tonykoop/ashiko-drum-workshop/images/05-glue-up-cherry-staves.jpg

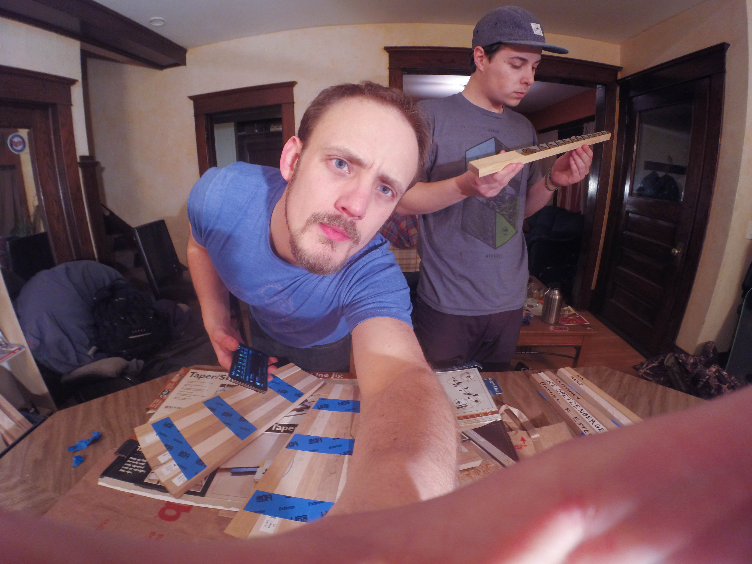
images/05-glue-up-cherry-staves.jpg
