tonykoop/ashiko-drum-workshop/images/05b-glue-up-clamping.jpg

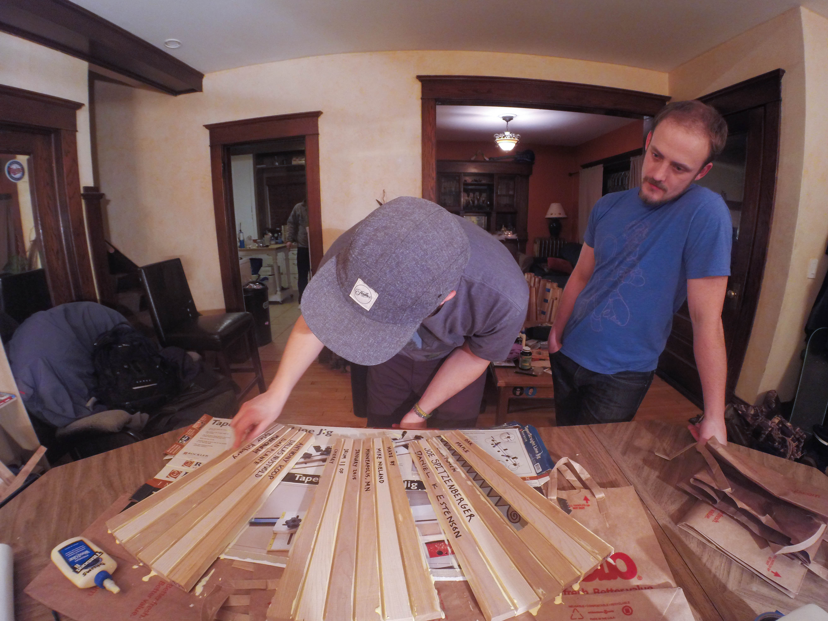
images/05b-glue-up-clamping.jpg
