tonykoop/ashiko-drum-workshop/images/2021-09-15 13.05.39.jpg

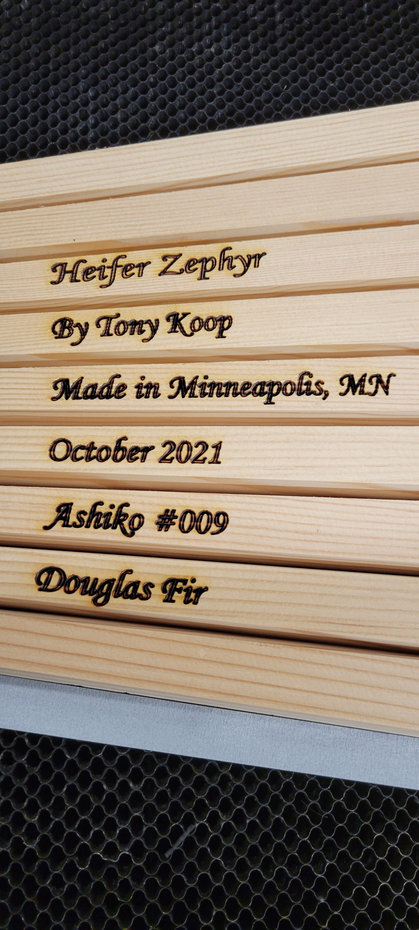
images/2021-09-15 13.05.39.jpg
