tonykoop/ashiko-drum-workshop/images/2021-10-07 13.28.02.jpg

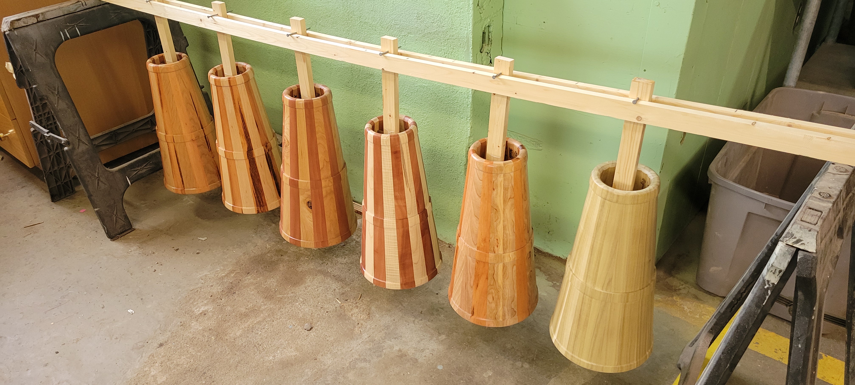
images/2021-10-07 13.28.02.jpg
