tonykoop/ashiko-drum-workshop/images/2021-10-21 14.14.43.jpg

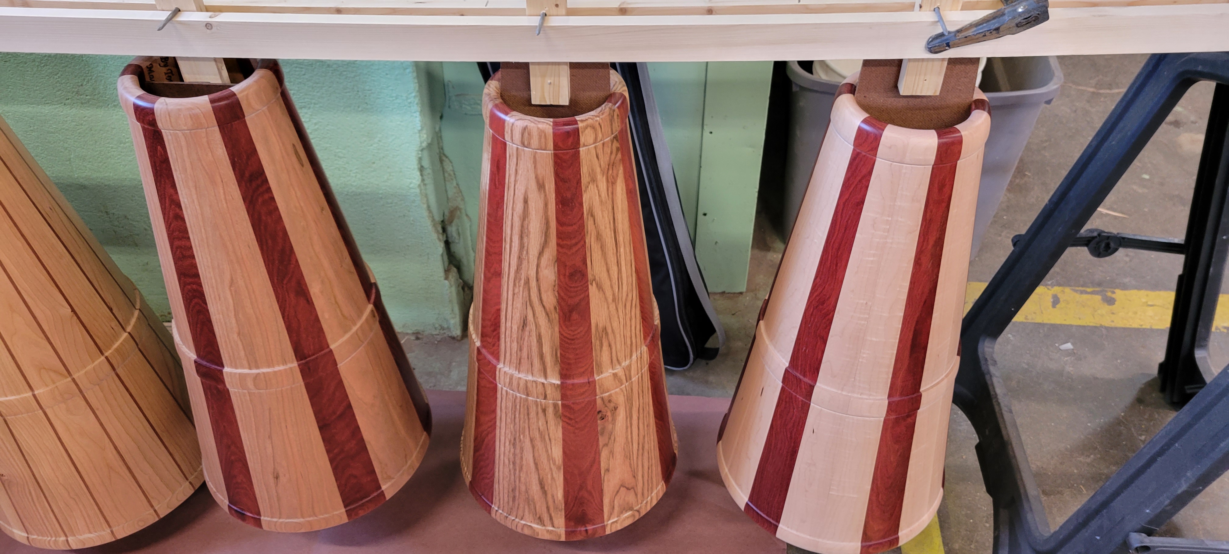
images/2021-10-21 14.14.43.jpg
