tonykoop/ashiko-drum-workshop/images/2021-10-22 16.16.47.jpg

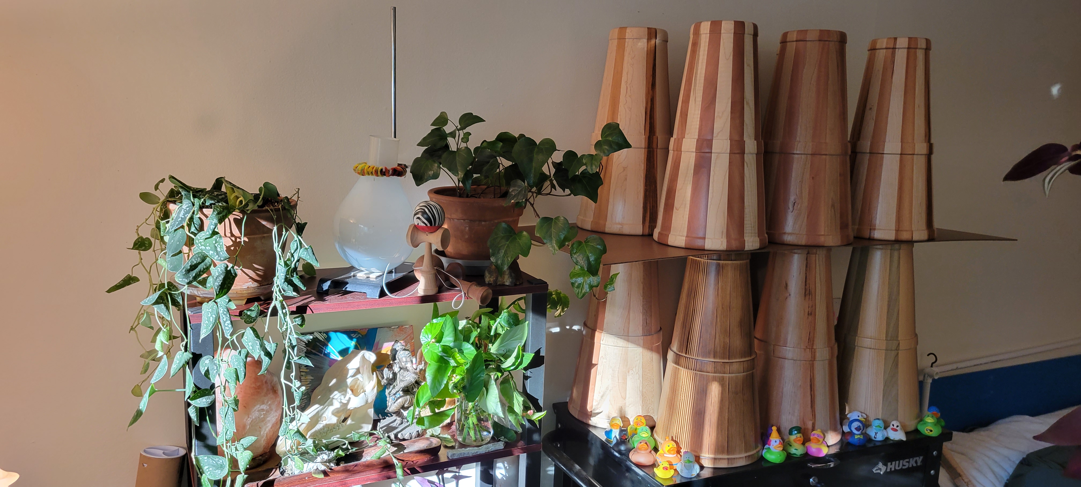
images/2021-10-22 16.16.47.jpg
