tonykoop/ashiko-drum-workshop/images/2021-10-22 16.17.06.jpg

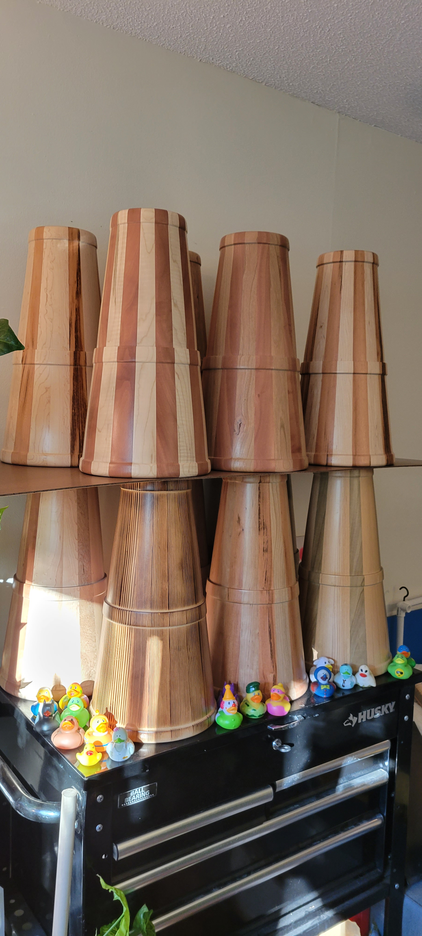
images/2021-10-22 16.17.06.jpg
