tonykoop/ashiko-drum-workshop/images/2021-12-14 12.53.09.jpg

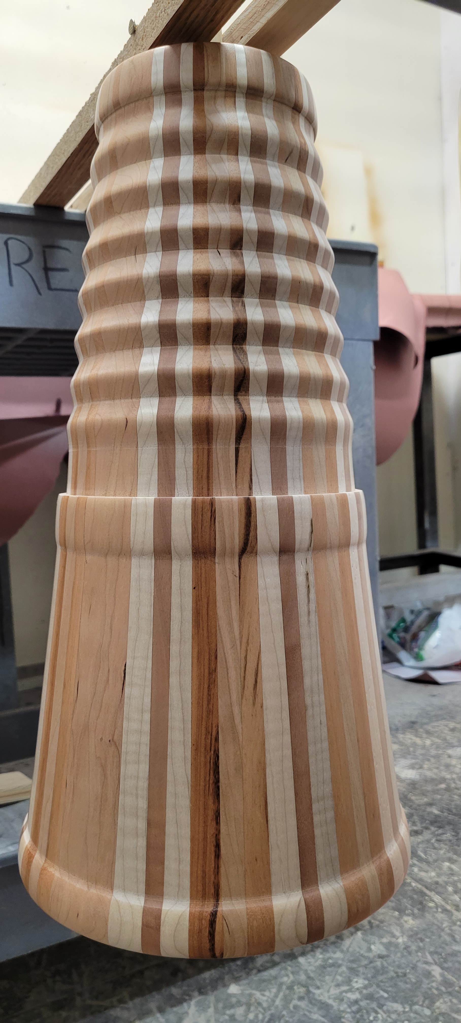
images/2021-12-14 12.53.09.jpg
