tonykoop/ashiko-drum-workshop/images/20211008_104015.jpg

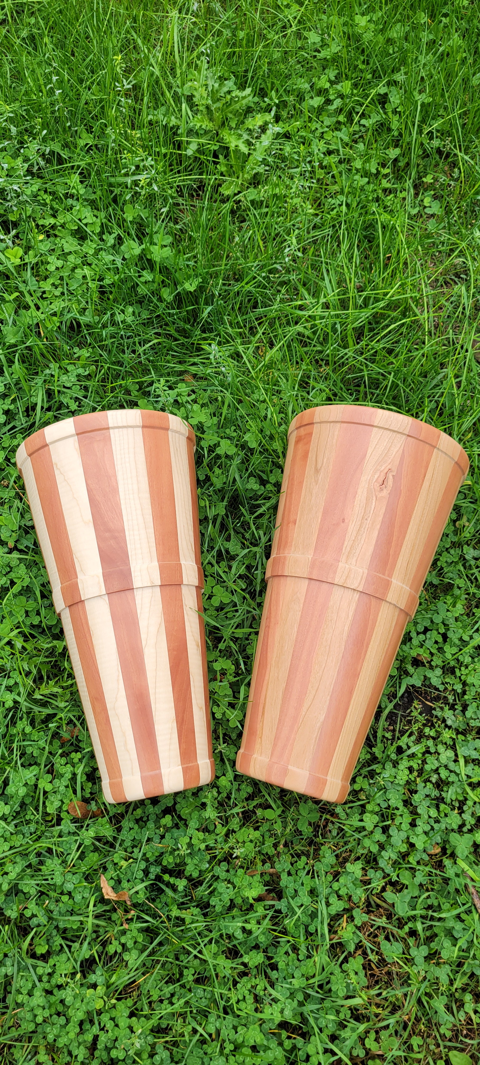
images/20211008_104015.jpg
