tonykoop/ashiko-drum-workshop/images/Ashiko Stave 3 Nesting.JPG

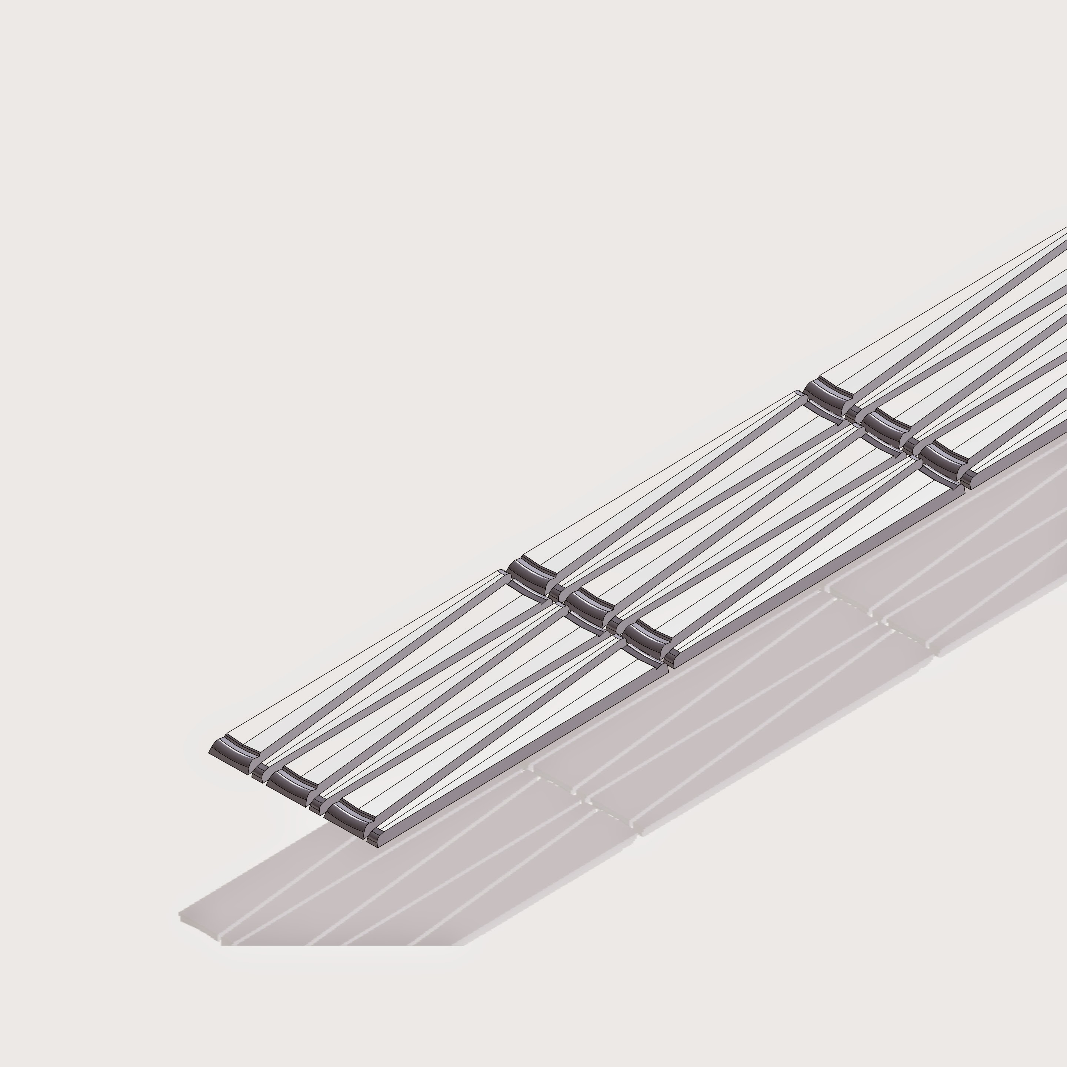
images/Ashiko Stave 3 Nesting.JPG
