tonykoop/ashiko-drum-workshop/images/figure-stave-labeling.png

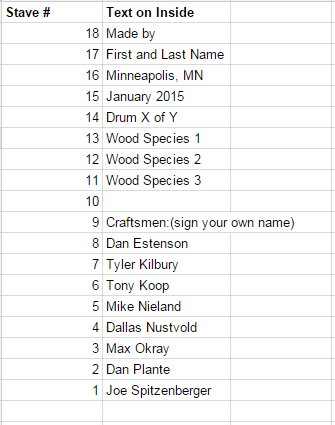
images/figure-stave-labeling.png
