tonykoop/ashiko-drum-workshop/images/Hack Factory Turning - Part 2 -1.JPG

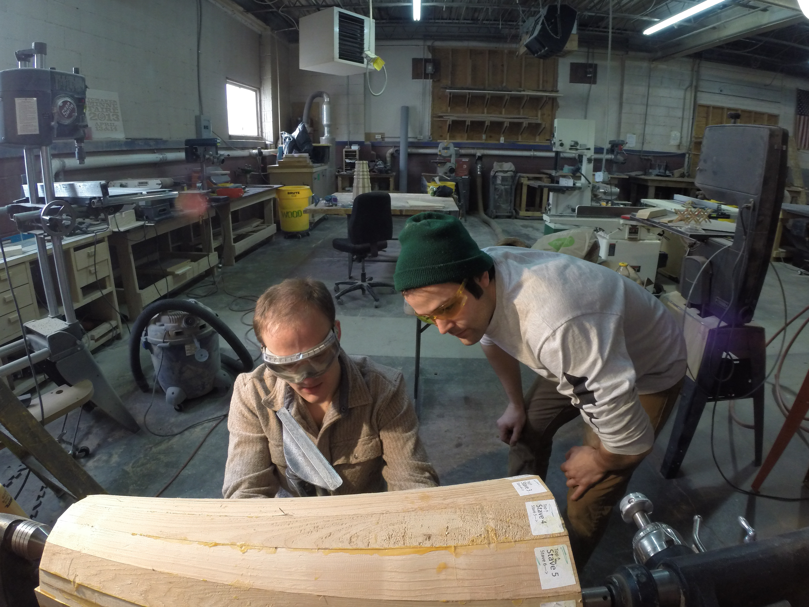
images/Hack Factory Turning - Part 2 -1.JPG
