tonykoop/ashiko-drum-workshop/images/Hack Factory Turning - Part 2 -23.JPG

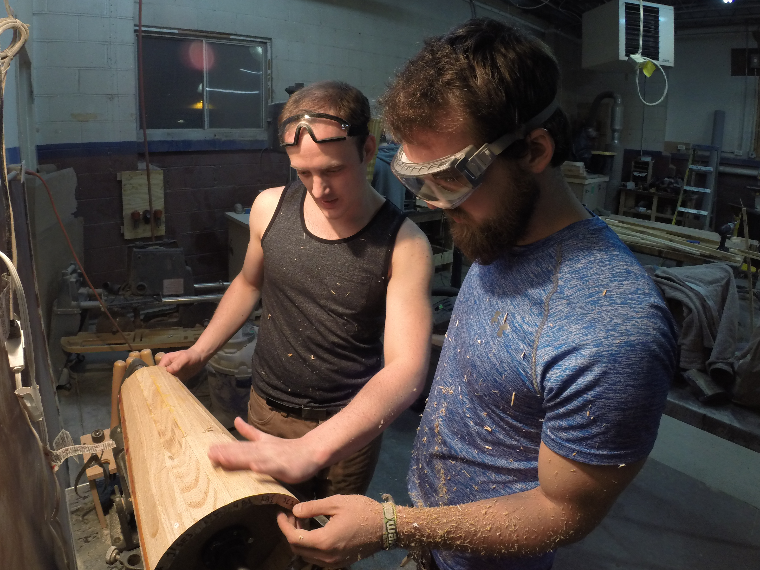
images/Hack Factory Turning - Part 2 -23.JPG
