tonykoop/ashiko-drum-workshop/images/Hack Factory Turning-49.JPG

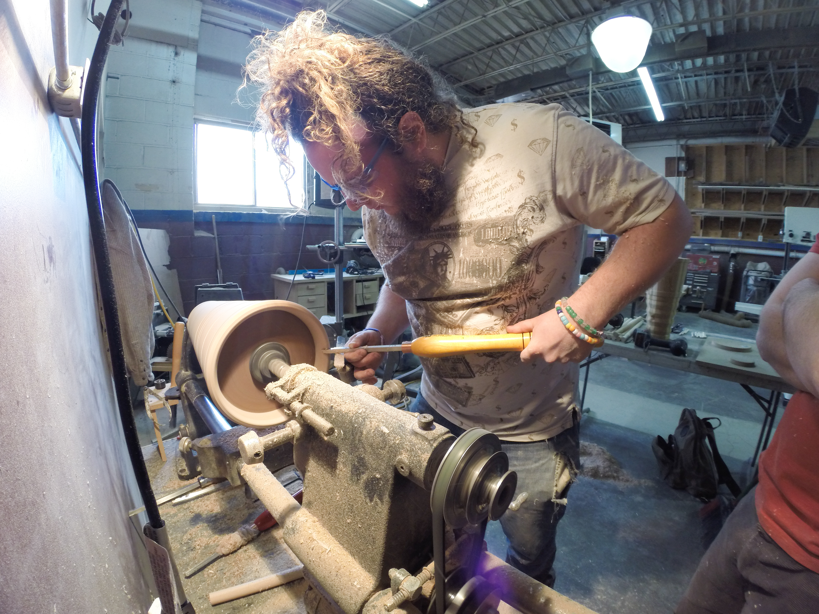
images/Hack Factory Turning-49.JPG
