tonykoop/ashiko-drum-workshop/images/IMG_20170116_170506.jpg

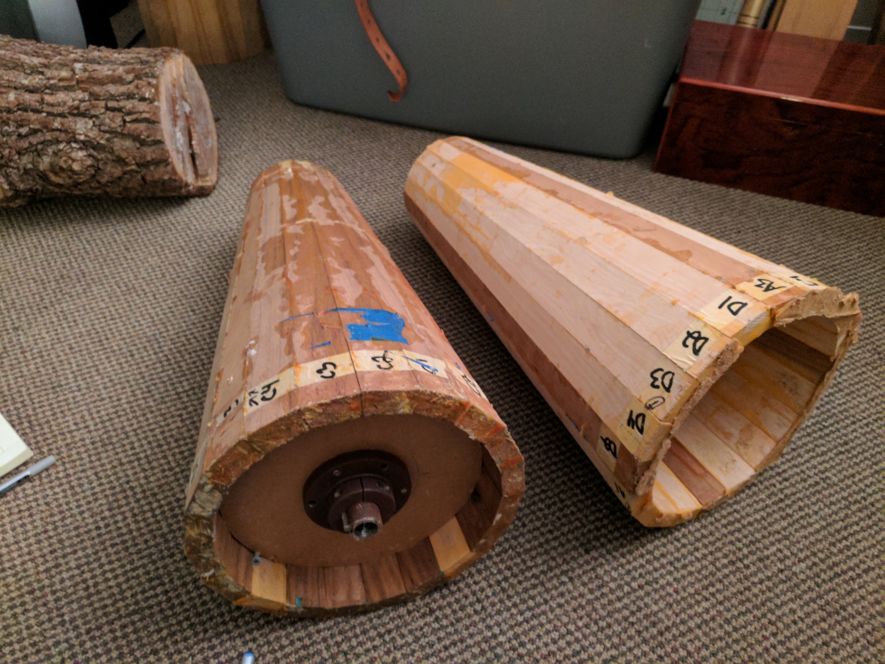
images/IMG_20170116_170506.jpg
