tonykoop/ashiko-drum-workshop/images/macro/multi-wood-stave-seams.png

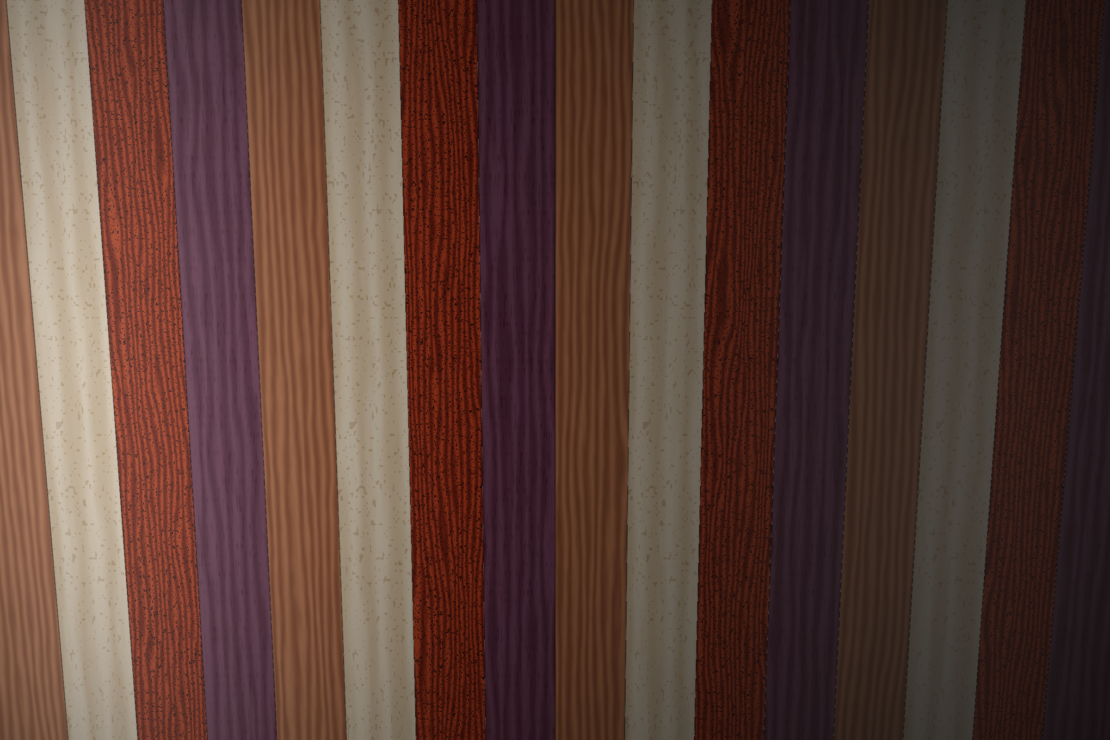
images/macro/multi-wood-stave-seams.png
