tonykoop/ashiko-drum-workshop/images/macro/rope-laced-goatskin-head.png

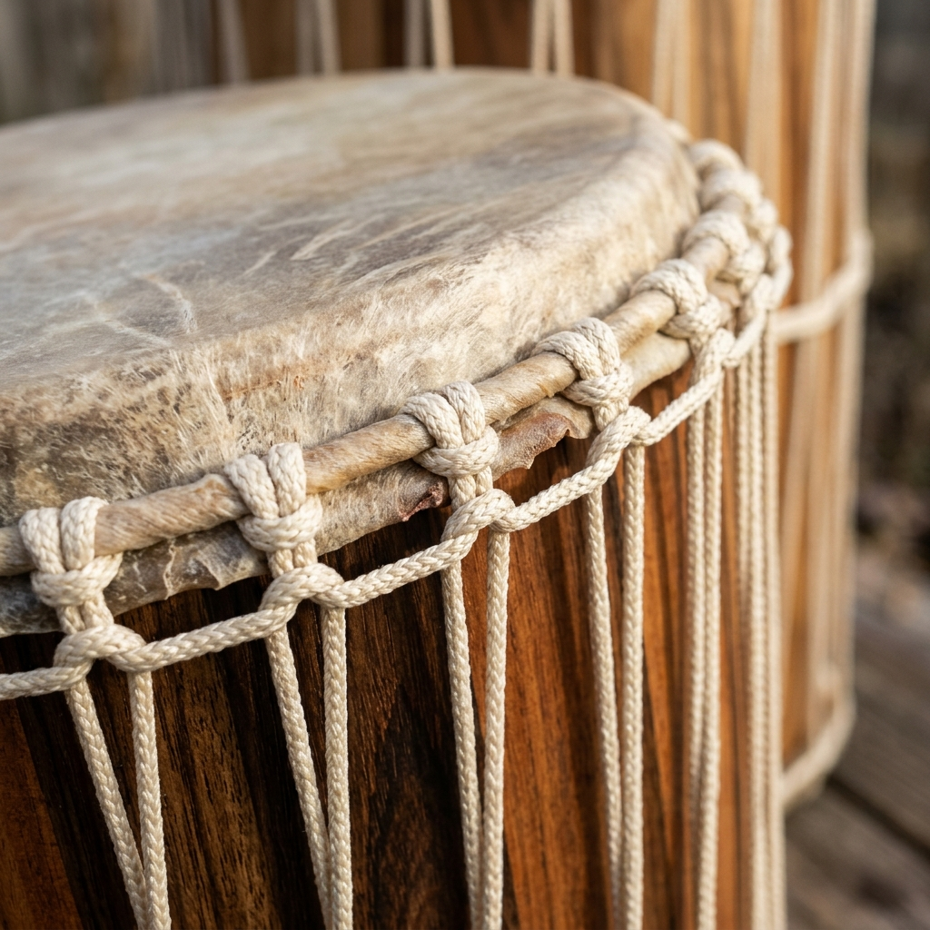
images/macro/rope-laced-goatskin-head.png
