tonykoop/ashiko-drum-workshop/images/Mike on Lathe-11.jpg

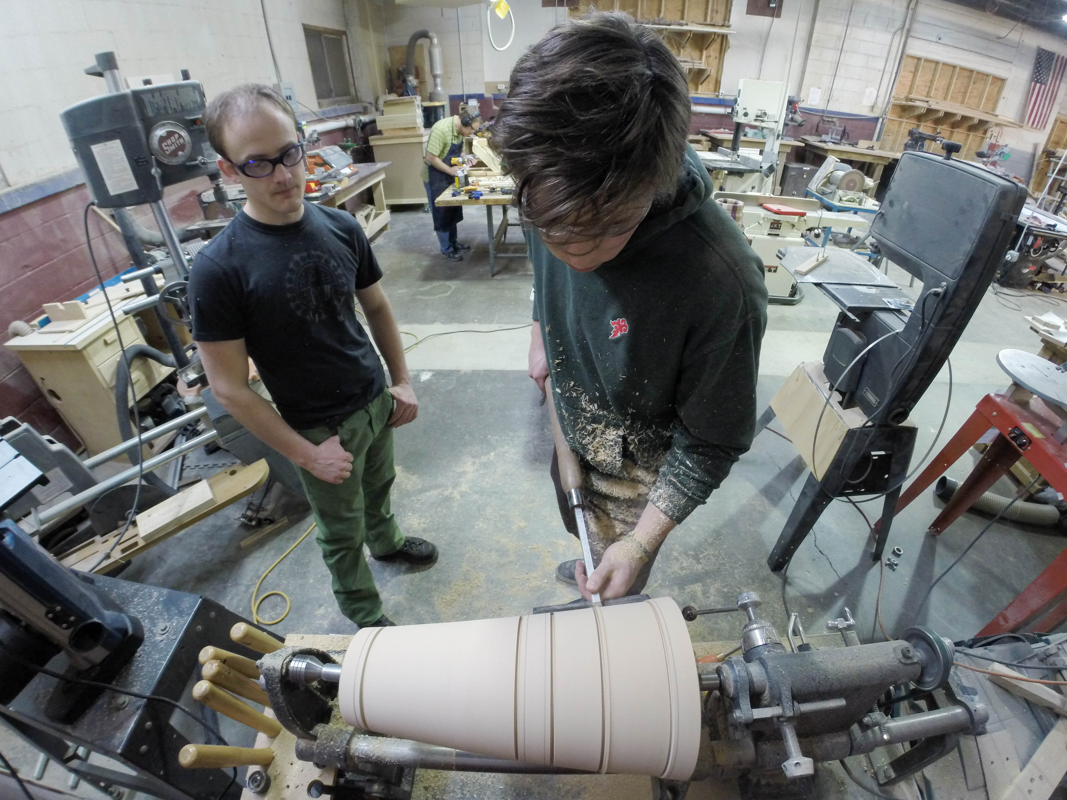
images/Mike on Lathe-11.jpg
