tonykoop/ashiko-drum-workshop/docs/Ashiko Makers Club/PDFs/Ashiko - BOM.pdf

Assembly Name :18 Stave Hardwood Ashiko | [42]
Serial Number:WFTH-55XXX-mmddyy-AA
Quote Date: | 11/19/2014
Estimated High Cost : | $158.00
Estimated Low Cost : | $77.50

# Ashiko Hand Drum

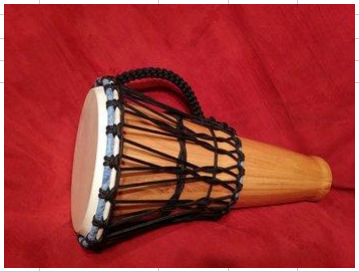
[picture p24: figure]

Part # Part Name | Description | Qty | Units | Picture | High Est | High Cost | Low Est | Low Cost

1

8/4 Hardwood
Lumber

Dried and surfaced
hardwood of various sorts
including domestic and
imported species.
5.3 | Board Feet | $ 10.00 | $ 53.00 | $ 5.00 | $ 26.50
2 | Steel Ring

Prefabricated 1/4" steel
ring. One small ring for the bottom and two larger rings for the top.
3 | Rings | $ 8.00 | $ 24.00 | $ 4.00 | $ 12.00
3 | Goat Skin

Hairless goat skin large
enough to fit the diameter of the drum head.
1 | Goat | $ 20.00 | $ 20.00 | $ 11.00 | $ 11.00
4 | Polyester Rope

3/16" double-braided
polyester with a lowstretch core, various color options available.
100 | Feet | $ 0.20 | $ 20.00 | $ 0.10 | $ 10.00
5 | Fabric

2" strip of decorative fabric used to wrap the top and
bottom steel rings.
60 | Inches | $ 0.10 | $ 6.00 | $ 0.05 | $ 3.00
6 | Supplies | Sandpaper, wood glue,
lacquer | 1 | $ 10.00 | $ 10.00 | $ 5.00 | $ 5.00

7

Shipping &
Handling | 1 | $ 25.00 | $ 25.00 | $ 10.00 | $ 10.00
Notes: | Total | $ 158.00 | $ 77.50
~Purchase lumber at Wood From The Hood
~The first four characters of the serial number decode as Wood From The Hood
followed by the 5 digit zip code where the wood originally grew, mmddyy is the date
the drum shell was glued together followed by the drum makers initials.
~Species available: Ash, Black Walnut, Butternut, Cherry, Elm
