tonykoop/ashiko-drum-workshop/docs/Ashiko Makers Club/PDFs/Bill of Materials V2.pdf

Assembly Name :18 Stave Hardwood Ashiko | [42]

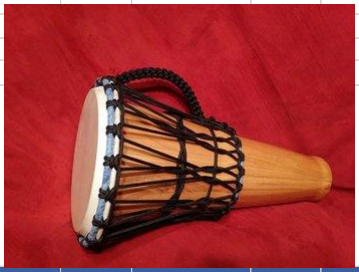
[picture p25: figure]

Quote Date: | 12/26/2014
Estimated Cost : | $78.00 | *

# Ashiko Hand Drum

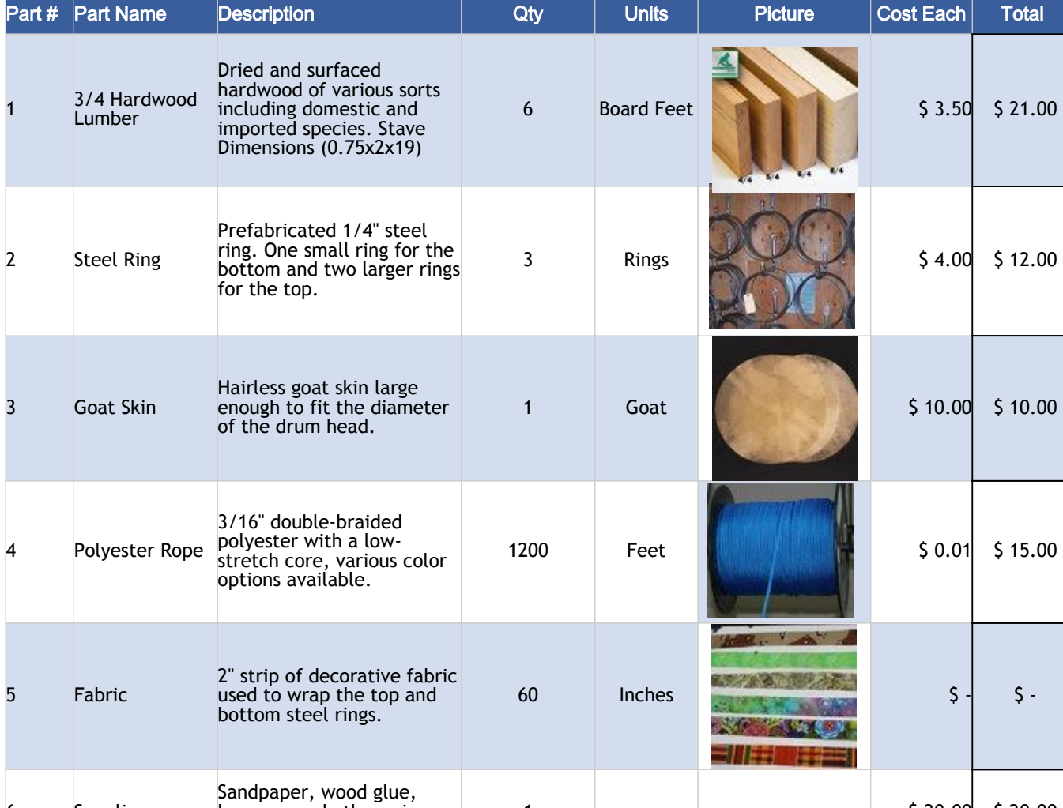
[picture p26: figure]
Part # Part Name; Description; Qty; Units; Picture; Cost Each; Total; 3/4 Hardwood Lumber; Dried and surfaced hardwood of various sorts including domestic and imported species. Stave Dimensions (0.75x2x19); Board Feet; Steel Ring; Prefabricated 1/4" steel ring. One small ring for the bottom and two larger rings for the top.; Rings; Goat Skin; Hairless goat skin large enough to fit the diameter of the drum head.; Goat; Polyester Rope; 3/16" double-braided polyester with a low- stretch core, various color options available.; Feet; Fabric; 2" strip of decorative fabric used to wrap the top and bottom steel rings.; Inches; Sandpaper, wood glue,

6 | Supplies

lacquer, and other misc
supplies.
1 | $ 20.00 | $ 20.00
Notes: | Total | $ 78.00
~3/4" Lumber Purchased @ Youngblood Lumber Company:
~5: Cherry (Ch) 5: Hard Maple (HM) | 1: Padauk (Pd) 1: Purple Heart (Ph)
*Price based on bulk discount of 7 or more assemblies using Hard Maple and/or Che
