tonykoop/ashiko-drum-workshop/docs/Ashiko Makers Club/Large Block of Wood.SLDPRT

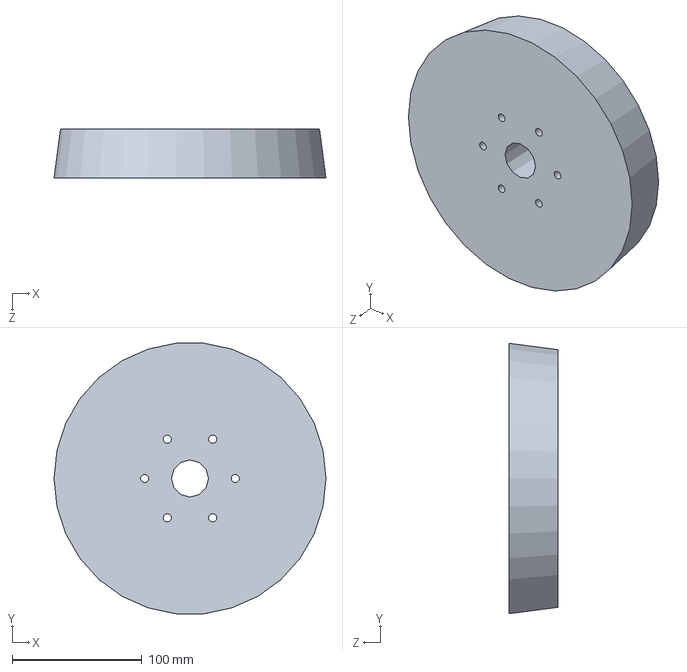
[picture p42: CAD file, 2026-05-23]
docs/Ashiko Makers Club/Large Block of Wood.SLDPRT
209.5 x 208.4 x 38.1 mm
