tonykoop/ashiko-drum-workshop/docs/Ashiko Makers Club/Spokes/16 Spoke.SLDPRT

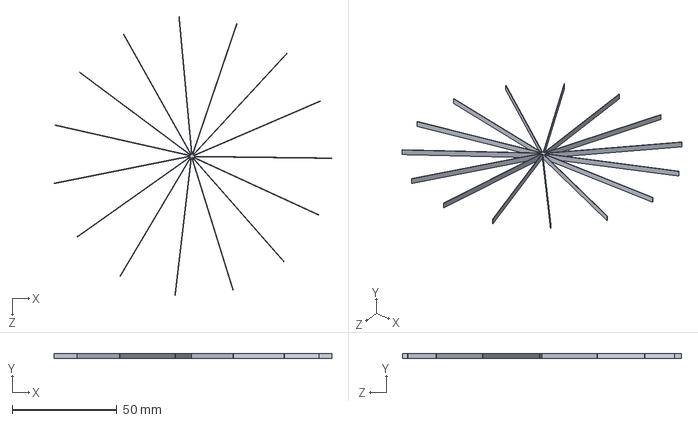
[picture p43: CAD file, 2026-05-23]
docs/Ashiko Makers Club/Spokes/16 Spoke.SLDPRT
132.8 x 2.54 x 133.3 mm
