tonykoop/ashiko-drum-workshop/docs/Ashiko Makers Club/To Print/Front Piece V4.STL

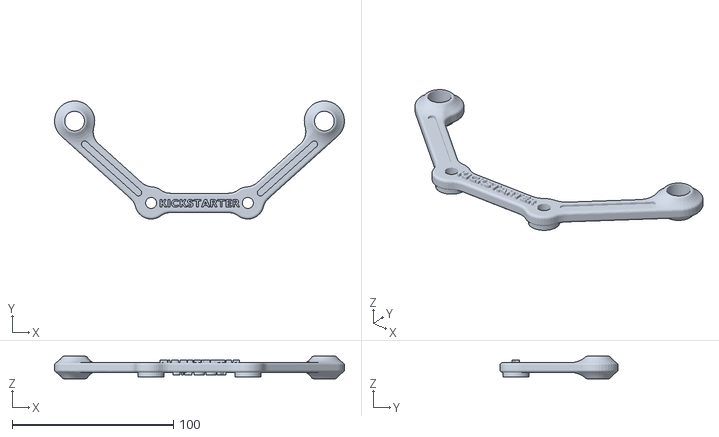
[picture p44: CAD file, 2026-05-23]
docs/Ashiko Makers Club/To Print/Front Piece V4.STL
180.0 x 73.3 x 14.0
