tonykoop/ashiko-drum-workshop/CAD/CNC Sled/Compound Taper Wedge Corrector.SLDPRT

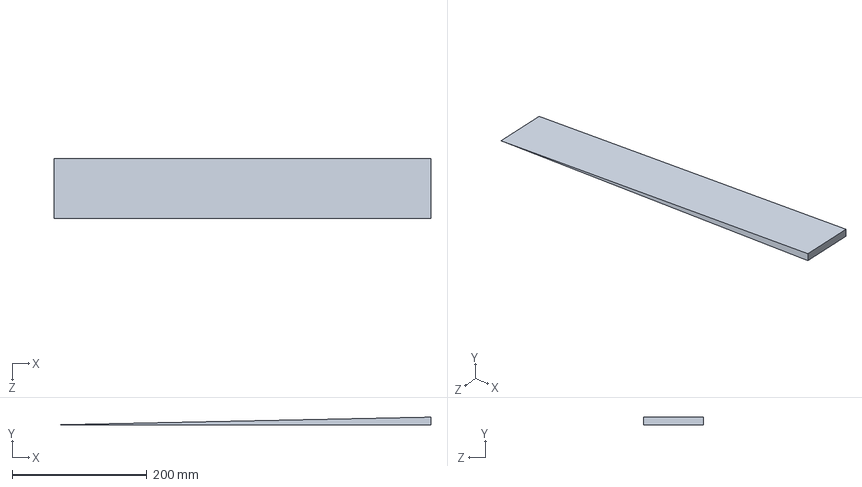
[picture p45: CAD file, 2026-05-23]
CAD/CNC Sled/Compound Taper Wedge Corrector.SLDPRT
558.8 x 11.5 x 88.9 mm
