tonykoop/ashiko-drum-workshop/docs/Ashiko Makers Club/Ashiko V3 REV010915 (Koops_Windows's conflicted copy 2015-01-16).SLDPRT

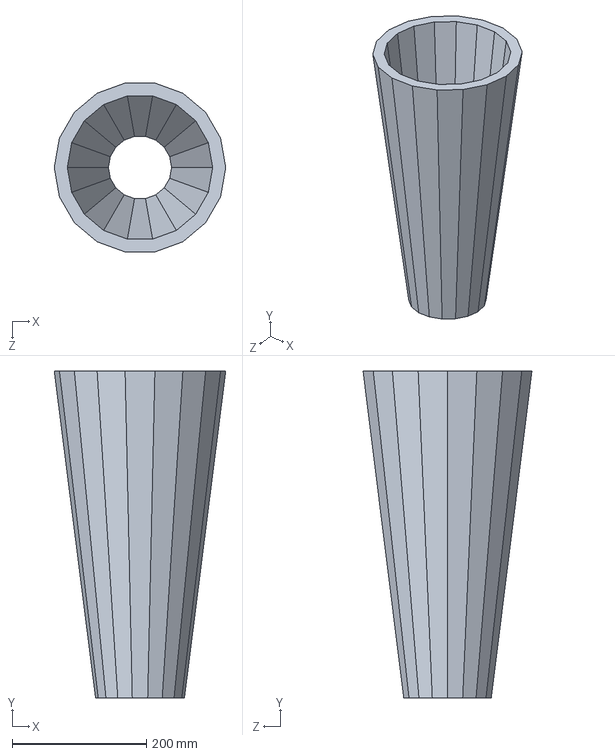
[picture p46: CAD file, 2026-05-23]
docs/Ashiko Makers Club/Ashiko V3 REV010915 (Koops_Windows's conflicted copy 2015-01-16).SLDPRT
256.0 x 488.0 x 252.1 mm
