tonykoop/ashiko-drum-workshop/docs/Ashiko Makers Club/Djembe/Djembe Joint Plate.SLDPRT

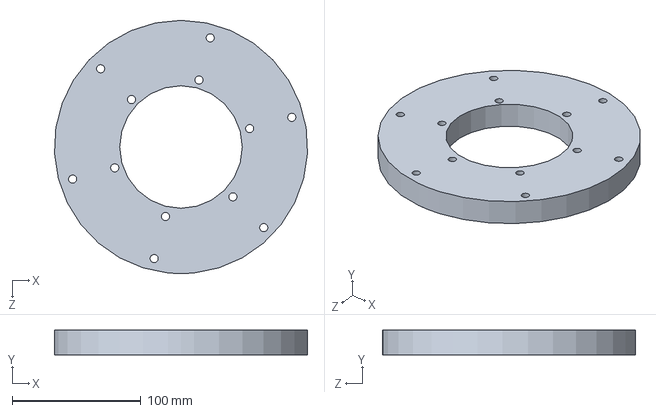
[picture p47: CAD file, 2026-05-23]
docs/Ashiko Makers Club/Djembe/Djembe Joint Plate.SLDPRT
196.6 x 19.1 x 196.9 mm
