tonykoop/ashiko-drum-workshop/docs/Ashiko Makers Club/To Print/Electronics Hub V3.STL

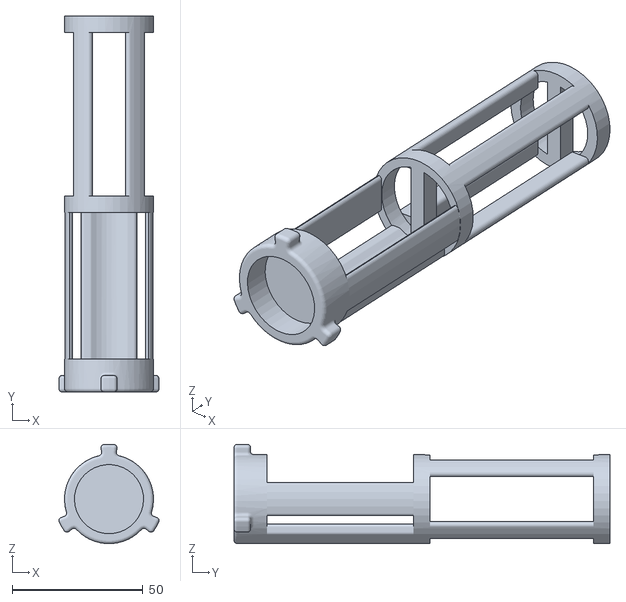
[picture p48: CAD file, 2026-05-23]
docs/Ashiko Makers Club/To Print/Electronics Hub V3.STL
38.3 x 143.8 x 38.0
