tonykoop/ashiko-drum-workshop/CAD/CNC Sled/Sled Rear A.SLDPRT

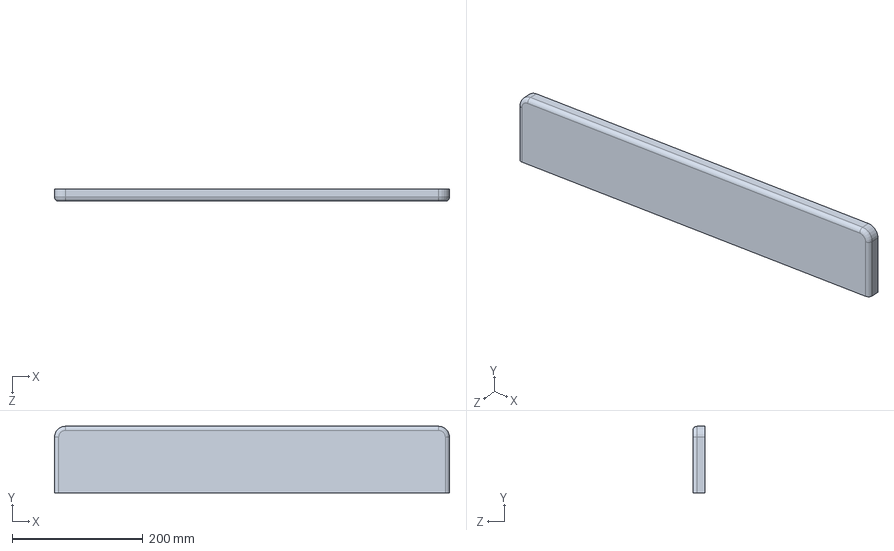
[picture p49: CAD file, 2026-05-23]
CAD/CNC Sled/Sled Rear A.SLDPRT
603.2 x 101.6 x 19.1 mm
