tonykoop/ashiko-drum-workshop/CAD/CNC Sled/Wedges/18 Segment Wedge.SLDPRT

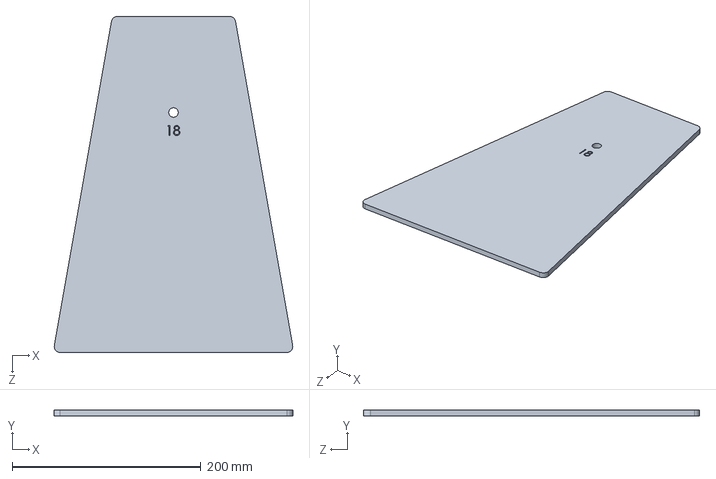
[picture p50: CAD file, 2026-05-23]
CAD/CNC Sled/Wedges/18 Segment Wedge.SLDPRT
252.5 x 5.99 x 355.6 mm
