tonykoop/ashiko-drum-workshop/docs/Ashiko Makers Club/To Print/Control Board Holder.STL

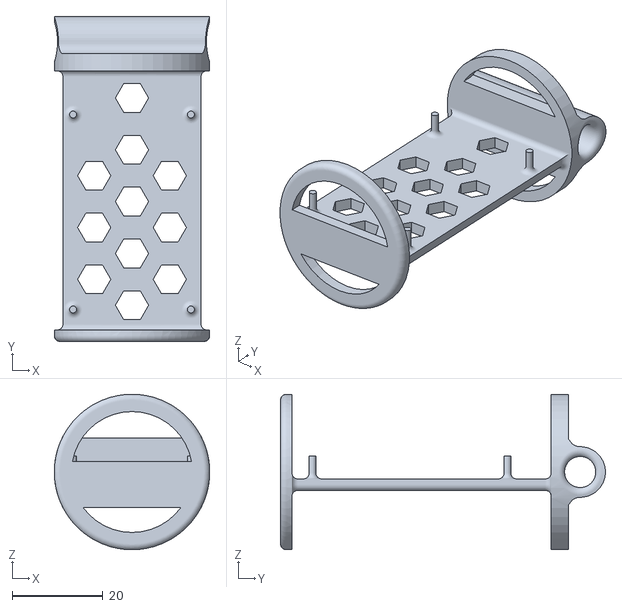
[picture p51: CAD file, 2026-05-23]
docs/Ashiko Makers Club/To Print/Control Board Holder.STL
34.3 x 71.7 x 34.3
