tonykoop/ashiko-drum-workshop/CAD/CNC Sled/3x20 Stave.SLDPRT

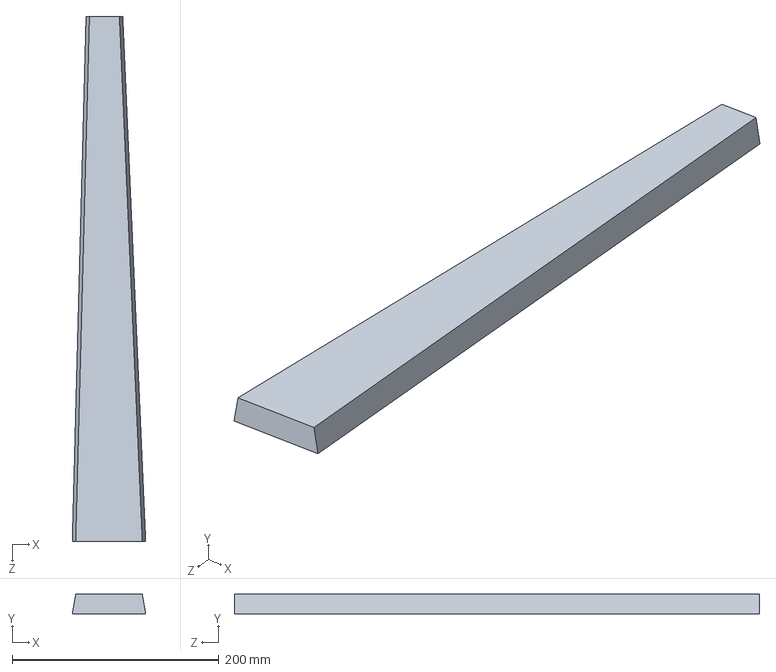
[picture p52: CAD file, 2026-05-23]
CAD/CNC Sled/3x20 Stave.SLDPRT
71.1 x 19.1 x 508.0 mm
