tonykoop/ashiko-drum-workshop/CAD/CNC Sled/Wedges/48 Segment Wedgie.SLDPRT

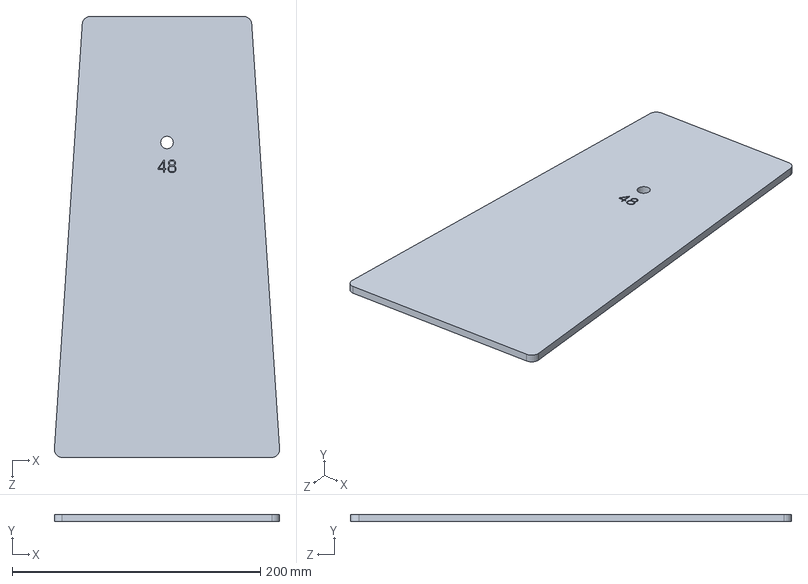
[picture p53: CAD file, 2026-05-23]
CAD/CNC Sled/Wedges/48 Segment Wedgie.SLDPRT
181.6 x 5.99 x 355.6 mm
