tonykoop/ashiko-drum-workshop/docs/Ashiko Makers Club/Djembe/Djembe Bottom REV013015.SLDPRT

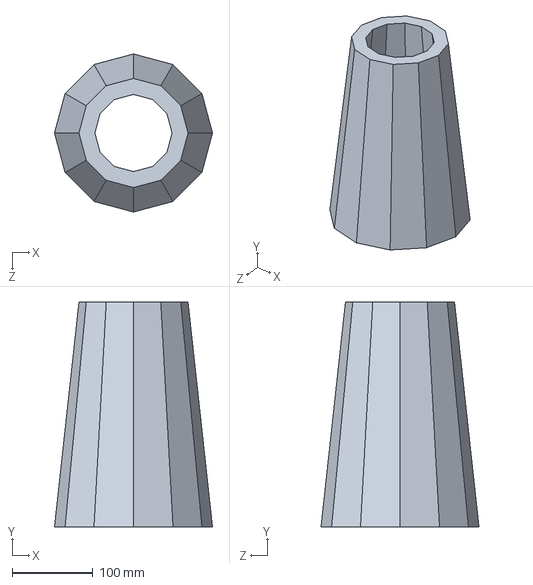
[picture p54: CAD file, 2026-05-23]
docs/Ashiko Makers Club/Djembe/Djembe Bottom REV013015.SLDPRT
196.3 x 279.4 x 196.3 mm
