tonykoop/ashiko-drum-workshop/docs/Ashiko Makers Club/To Print/Rod V4.STL

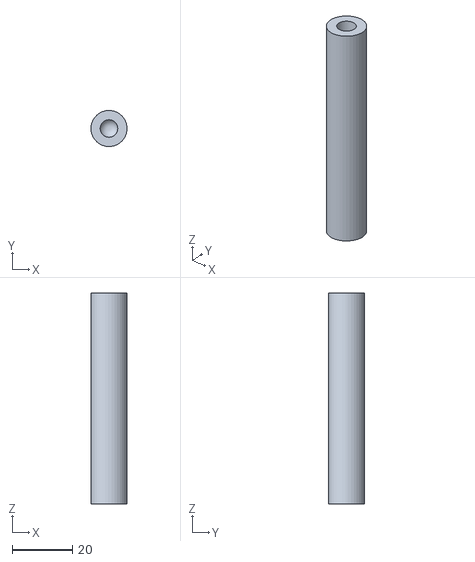
[picture p55: CAD file, 2026-05-23]
docs/Ashiko Makers Club/To Print/Rod V4.STL
12.0 x 12.0 x 70.0
