tonykoop/ashiko-drum-workshop/CAD/CNC Sled/Taper Wedge - 10 degree 18 stave shell.SLDPRT

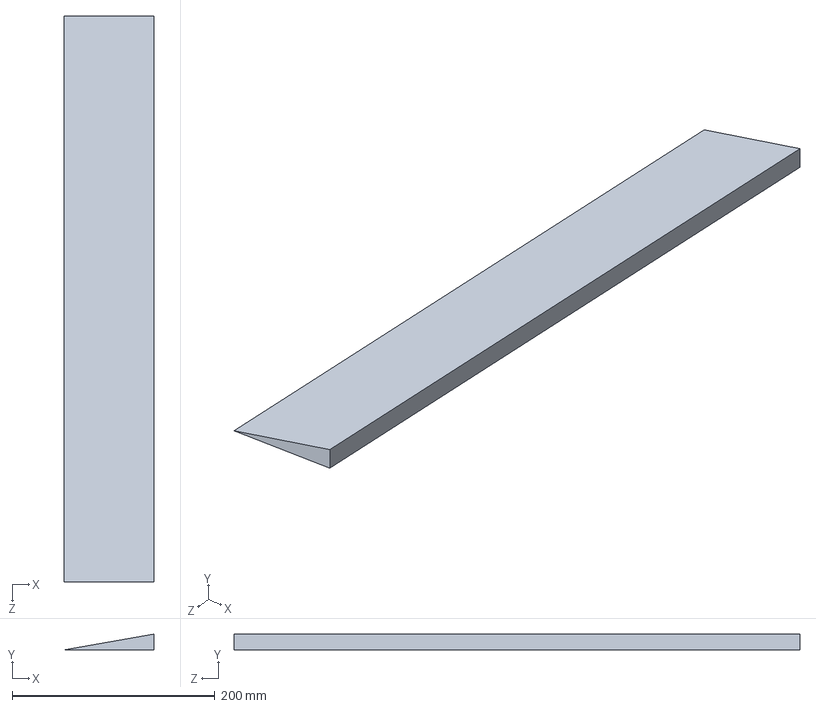
[picture p56: CAD file, 2026-05-23]
CAD/CNC Sled/Taper Wedge - 10 degree 18 stave shell.SLDPRT
88.9 x 15.7 x 558.8 mm
