tonykoop/ashiko-drum-workshop/CAD/CNC Sled/Wedges/Universal Wedge B.SLDPRT

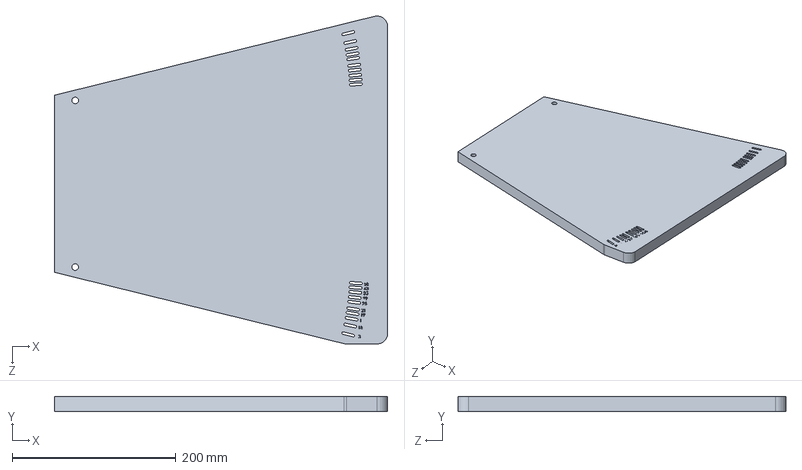
[picture p57: CAD file, 2026-05-23]
CAD/CNC Sled/Wedges/Universal Wedge B.SLDPRT
406.4 x 18.0 x 400.0 mm
