tonykoop/ashiko-drum-workshop/CAD/CNC Sled/CrossCut Arm B.SLDPRT

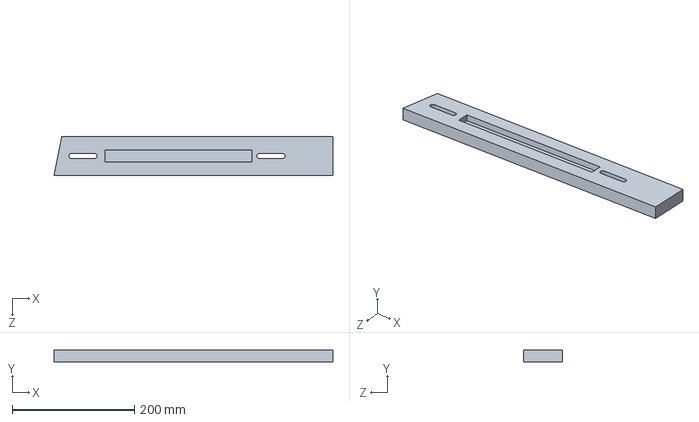
[picture p58: CAD file, 2026-05-23]
CAD/CNC Sled/CrossCut Arm B.SLDPRT
457.2 x 19.1 x 63.5 mm
