tonykoop/ashiko-drum-workshop/CAD/CNC Sled/Wedges/30 Segment Wedge.SLDPRT

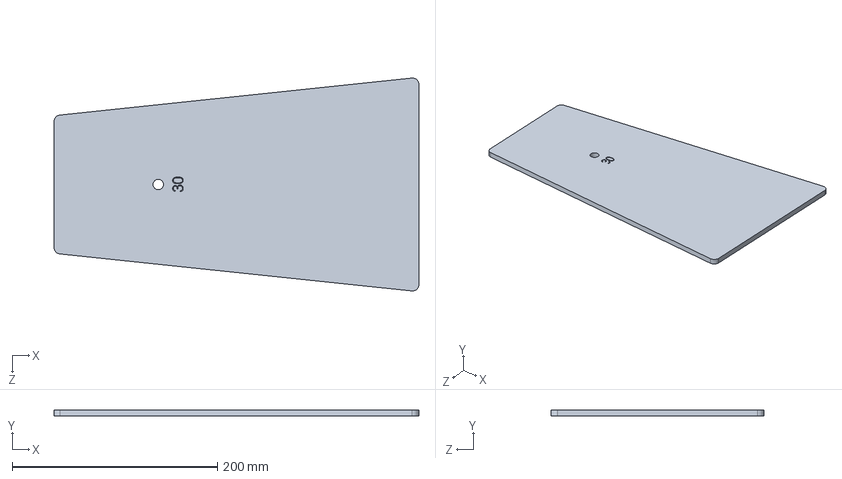
[picture p59: CAD file, 2026-05-23]
CAD/CNC Sled/Wedges/30 Segment Wedge.SLDPRT
355.6 x 5.99 x 207.4 mm
