tonykoop/ashiko-drum-workshop/docs/Ashiko Makers Club/Djembe/Djembe - 16 Stave.SLDPRT

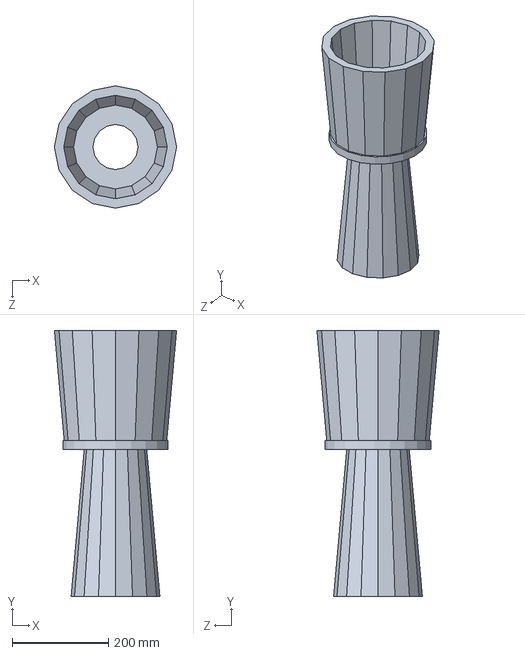
[picture p60: CAD file, 2026-05-23]
docs/Ashiko Makers Club/Djembe/Djembe - 16 Stave.SLDPRT
253.9 x 552.5 x 253.9 mm
