tonykoop/ashiko-drum-workshop/CAD/CNC Sled/Sled Rear B.SLDPRT

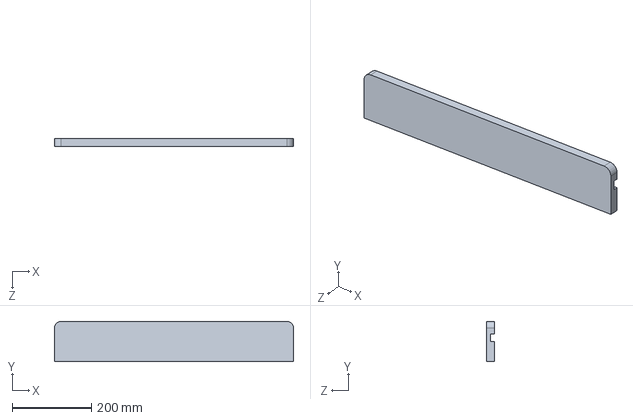
[picture p61: CAD file, 2026-05-23]
CAD/CNC Sled/Sled Rear B.SLDPRT
603.2 x 101.6 x 19.1 mm
