tonykoop/ashiko-drum-workshop/CAD/CNC Sled/Wedges/Universal Wedge.SLDPRT

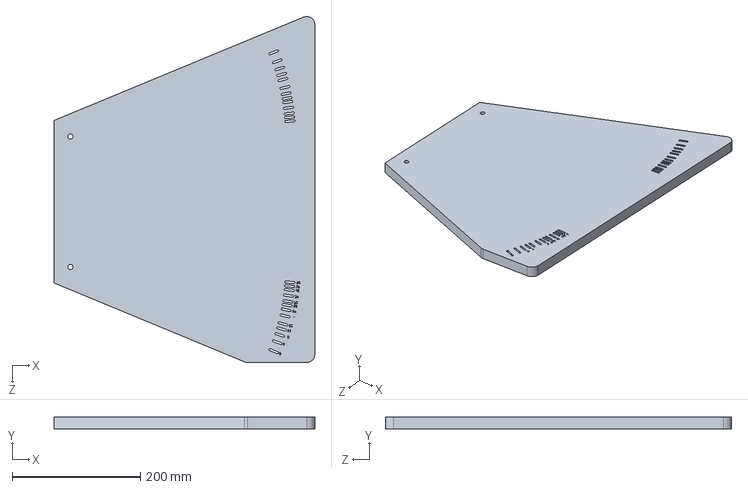
[picture p62: CAD file, 2026-05-23]
CAD/CNC Sled/Wedges/Universal Wedge.SLDPRT
406.4 x 18.0 x 539.1 mm
