tonykoop/ashiko-drum-workshop/CAD/CNC Sled/Ashiko Stave REV012316.SLDPRT

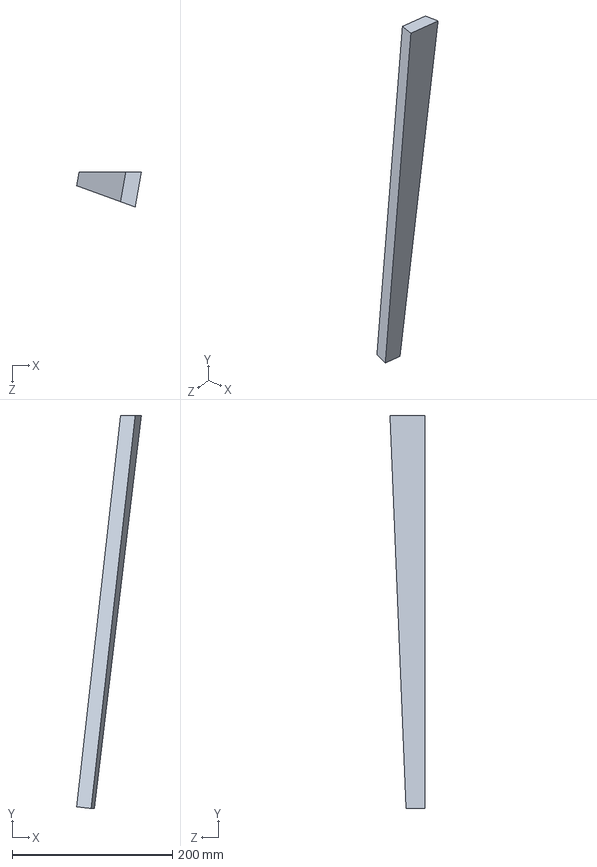
[picture p63: CAD file, 2026-05-23]
CAD/CNC Sled/Ashiko Stave REV012316.SLDPRT
80.8 x 490.2 x 43.8 mm
