tonykoop/ashiko-drum-workshop/CAD/CNC Sled/Wedges/40 Segment Wedge.SLDPRT

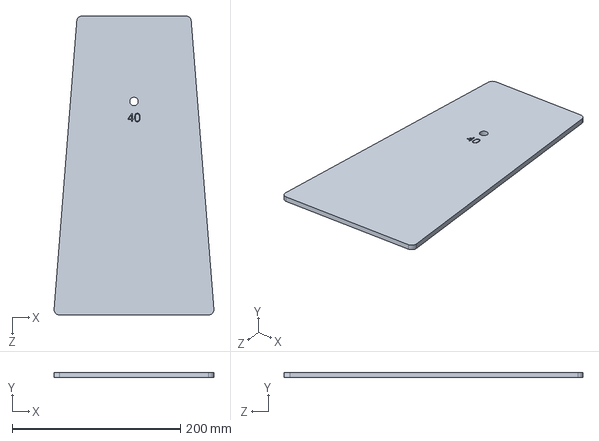
[picture p64: CAD file, 2026-05-23]
CAD/CNC Sled/Wedges/40 Segment Wedge.SLDPRT
190.1 x 5.99 x 355.6 mm
