tonykoop/ashiko-drum-workshop/docs/Ashiko Makers Club/Djembe/Djembe Top - V2.SLDPRT

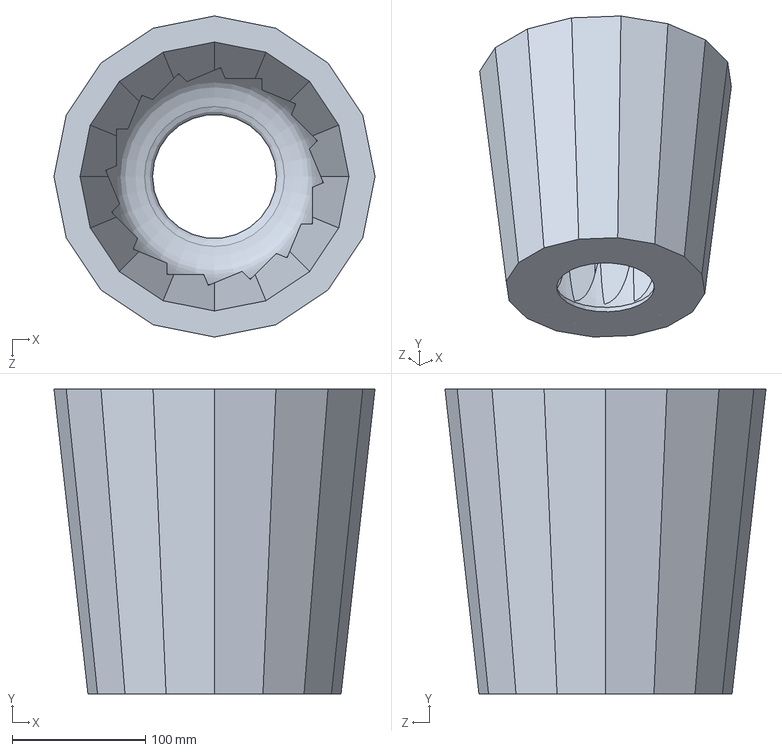
[picture p65: CAD file, 2026-05-23]
docs/Ashiko Makers Club/Djembe/Djembe Top - V2.SLDPRT
240.9 x 228.6 x 240.9 mm
