tonykoop/ashiko-drum-workshop/docs/Ashiko Makers Club/Small Block of Wood.SLDPRT

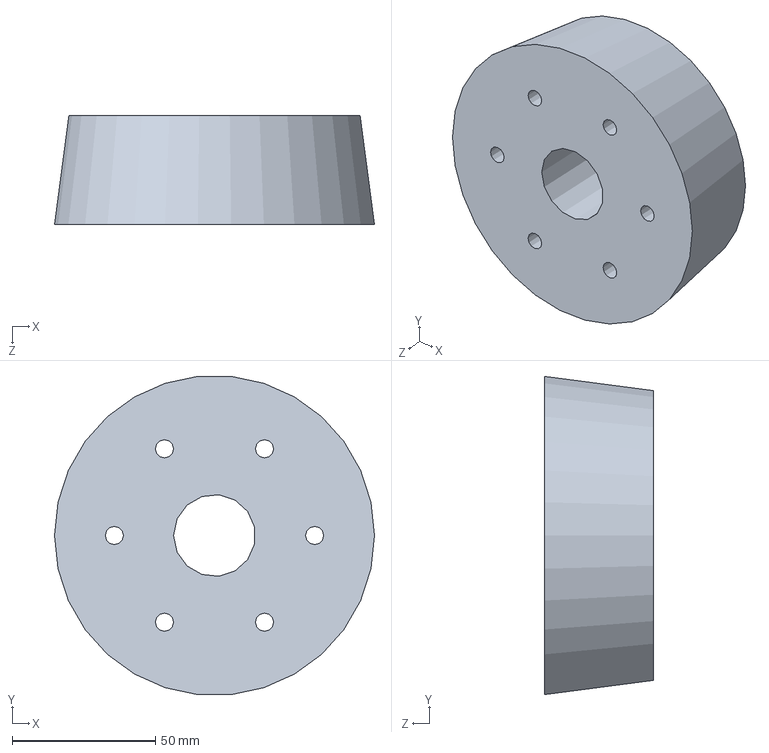
[picture p66: CAD file, 2026-05-23]
docs/Ashiko Makers Club/Small Block of Wood.SLDPRT
111.6 x 111.0 x 38.1 mm
