tonykoop/ashiko-drum-workshop/CAD/CNC Sled/Taper Arm.SLDPRT

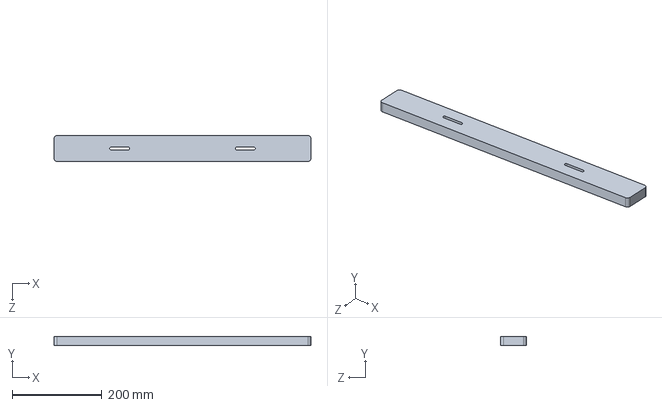
[picture p67: CAD file, 2026-05-23]
CAD/CNC Sled/Taper Arm.SLDPRT
571.5 x 19.1 x 57.1 mm
