tonykoop/ashiko-drum-workshop/CAD/CNC Sled/Wedges/12 Segment Wedgie.SLDPRT

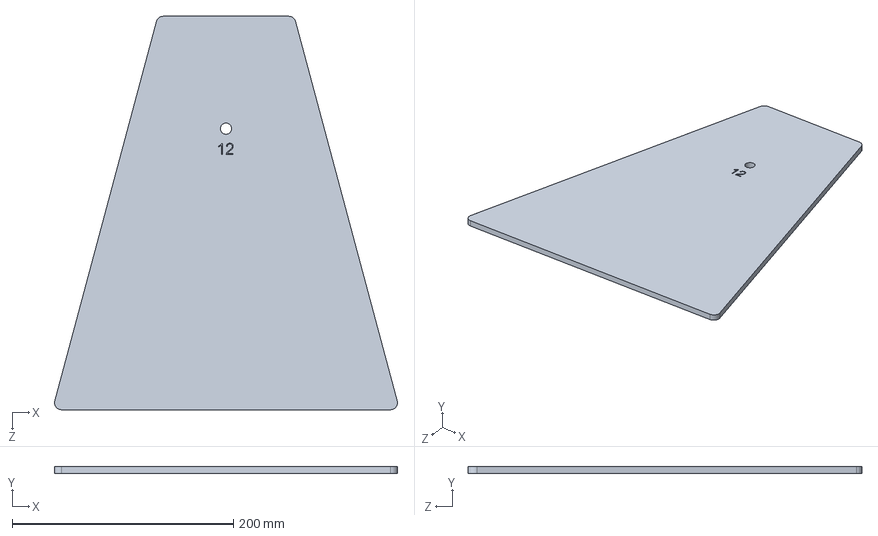
[picture p68: CAD file, 2026-05-23]
CAD/CNC Sled/Wedges/12 Segment Wedgie.SLDPRT
309.9 x 5.99 x 355.6 mm
