tonykoop/ashiko-drum-workshop/docs/Ashiko Makers Club/Djembe/Djembe Top REV013015.SLDPRT

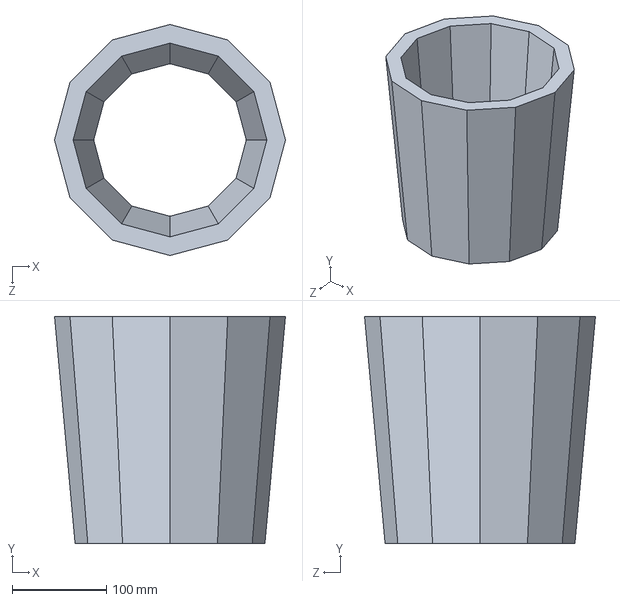
[picture p69: CAD file, 2026-05-23]
docs/Ashiko Makers Club/Djembe/Djembe Top REV013015.SLDPRT
245.3 x 241.3 x 245.3 mm
