tonykoop/ashiko-drum-workshop/docs/Ashiko Makers Club/Small Wood Block.SLDPRT

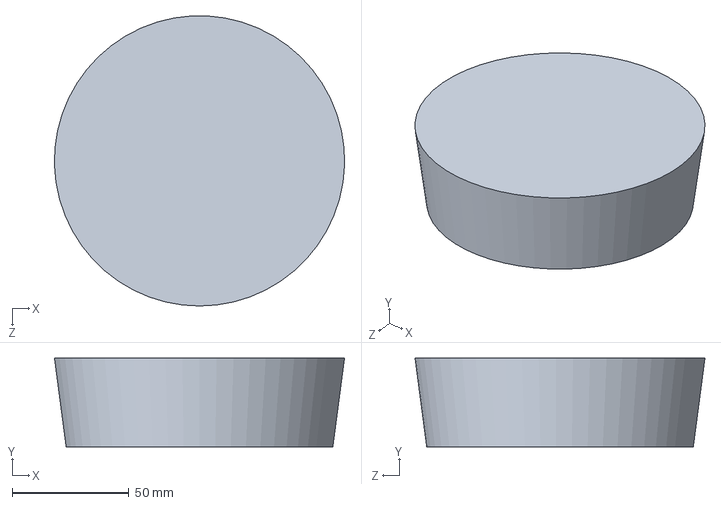
[picture p70: CAD file, 2026-05-23]
docs/Ashiko Makers Club/Small Wood Block.SLDPRT
124.3 x 38.1 x 124.2 mm
