tonykoop/ashiko-drum-workshop/docs/Ashiko Makers Club/Djembe/Djembe Bottom - V2.SLDPRT

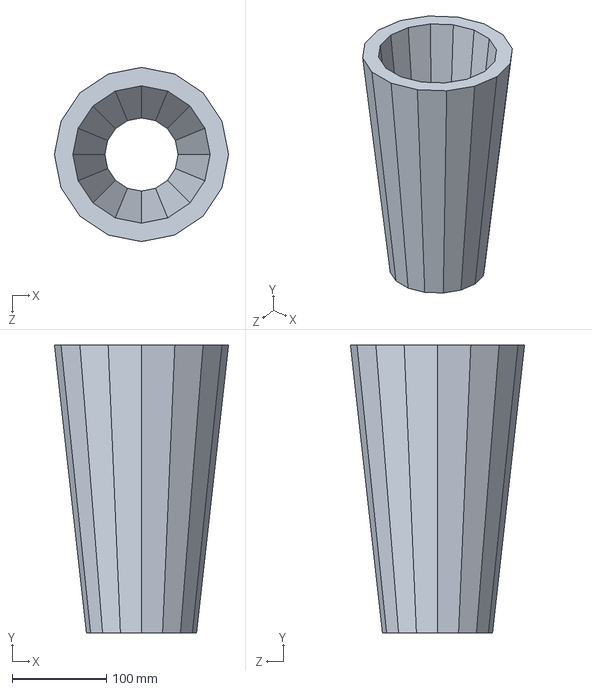
[picture p71: CAD file, 2026-05-23]
docs/Ashiko Makers Club/Djembe/Djembe Bottom - V2.SLDPRT
184.4 x 304.8 x 184.4 mm
