tonykoop/ashiko-drum-workshop/CAD/CNC Sled/18 Stave Cartridge.SLDPRT

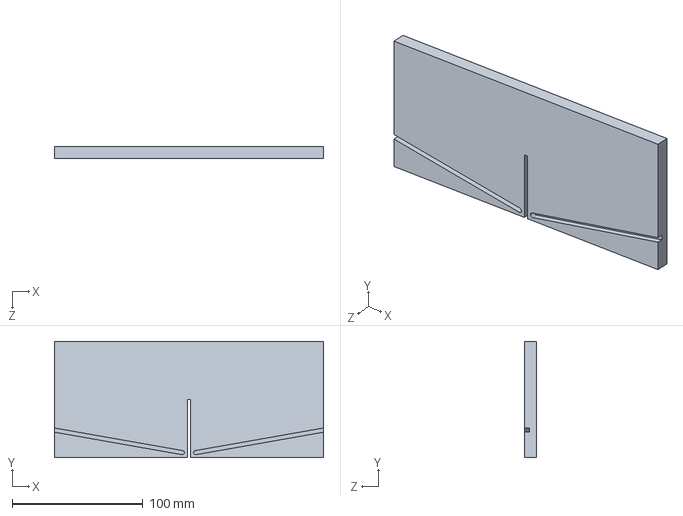
[picture p72: CAD file, 2026-05-23]
CAD/CNC Sled/18 Stave Cartridge.SLDPRT
205.7 x 88.9 x 8.99 mm
