tonykoop/ashiko-drum-workshop/CAD/CNC Sled/Wedges/24 Segment Wedgie.SLDPRT

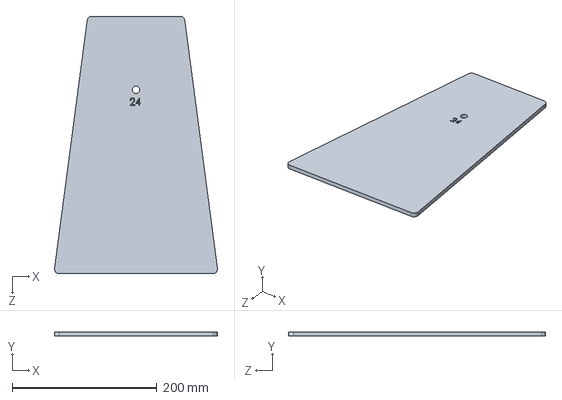
[picture p73: CAD file, 2026-05-23]
CAD/CNC Sled/Wedges/24 Segment Wedgie.SLDPRT
225.1 x 5.99 x 355.6 mm
