tonykoop/ashiko-drum-workshop/docs/Ashiko Makers Club/Djembe/Djembe REV040215.SLDPRT

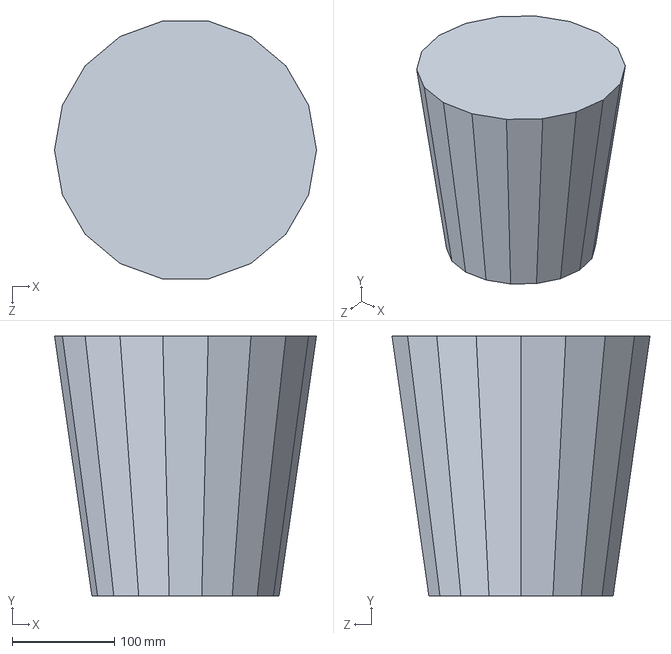
[picture p74: CAD file, 2026-05-23]
docs/Ashiko Makers Club/Djembe/Djembe REV040215.SLDPRT
256.0 x 254.0 x 252.1 mm
