tonykoop/ashiko-drum-workshop/CAD/CNC Sled/Sled Bottom.SLDPRT

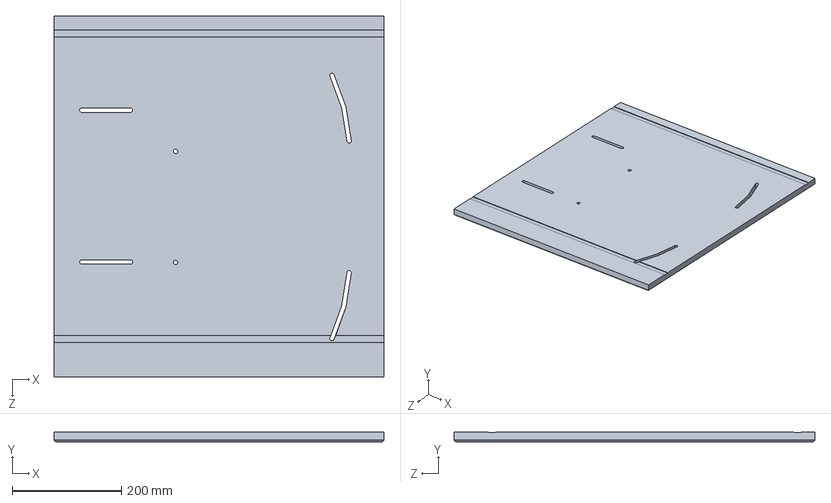
[picture p75: CAD file, 2026-05-23]
CAD/CNC Sled/Sled Bottom.SLDPRT
603.2 x 19.1 x 660.4 mm
