tonykoop/ashiko-drum-workshop/CAD/CNC Sled/Wedges/8 Segment Wedgie.SLDPRT

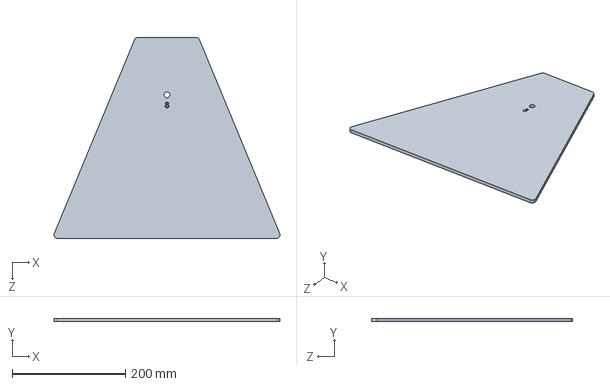
[picture p76: CAD file, 2026-05-23]
CAD/CNC Sled/Wedges/8 Segment Wedgie.SLDPRT
400.0 x 5.99 x 355.6 mm
