tonykoop/ashiko-drum-workshop/docs/Ashiko Makers Club/Large Wood Block.SLDPRT

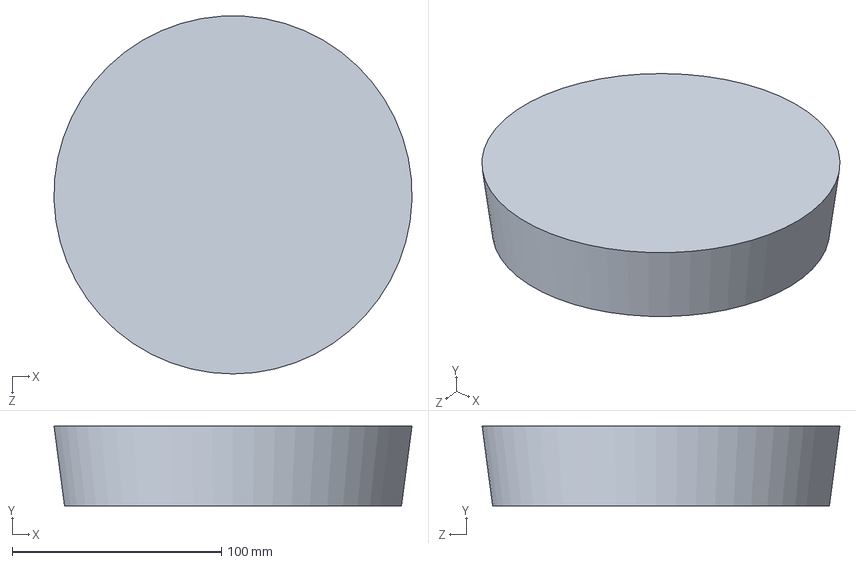
[picture p77: CAD file, 2026-05-23]
docs/Ashiko Makers Club/Large Wood Block.SLDPRT
171.0 x 38.1 x 170.9 mm
