tonykoop/ashiko-drum-workshop/CAD/CNC Sled/Sliding Track.SLDPRT

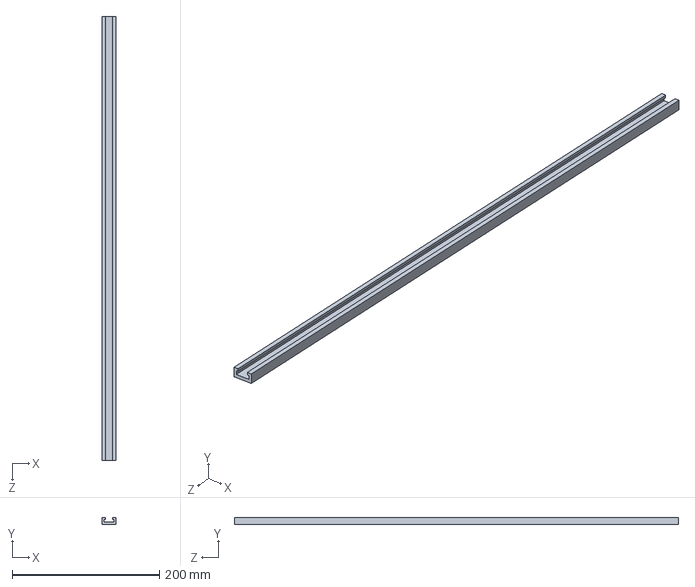
[picture p78: CAD file, 2026-05-23]
CAD/CNC Sled/Sliding Track.SLDPRT
19.1 x 9.53 x 603.2 mm
