tonykoop/ashiko-drum-workshop/CAD/CNC Sled/Wedges/32 Segment Wedge.SLDPRT

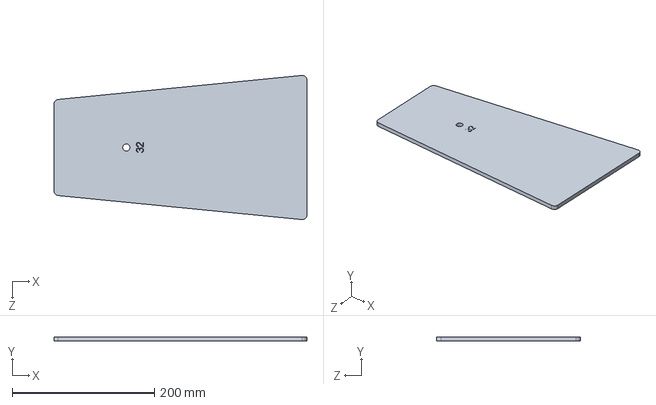
[picture p79: CAD file, 2026-05-23]
CAD/CNC Sled/Wedges/32 Segment Wedge.SLDPRT
355.6 x 5.99 x 202.7 mm
