tonykoop/ashiko-drum-workshop/docs/Ashiko Makers Club/19in Stave V3.SLDPRT

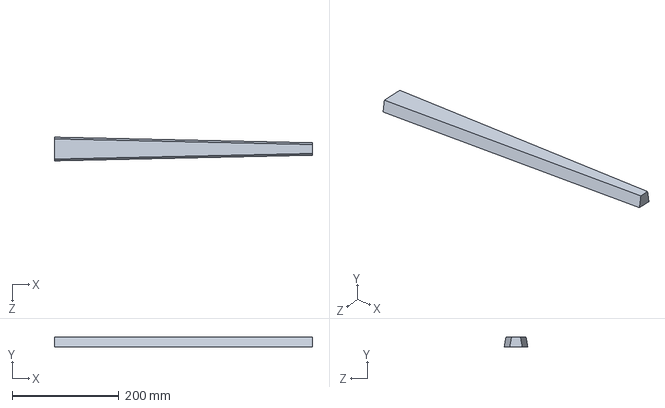
[picture p80: CAD file, 2026-04-25]
docs/Ashiko Makers Club/19in Stave V3.SLDPRT
482.6 x 19.1 x 44.5 mm
