tonykoop/ashiko-drum-workshop/CAD/CNC Sled/Wedges/36 Segment Wedgie.SLDPRT

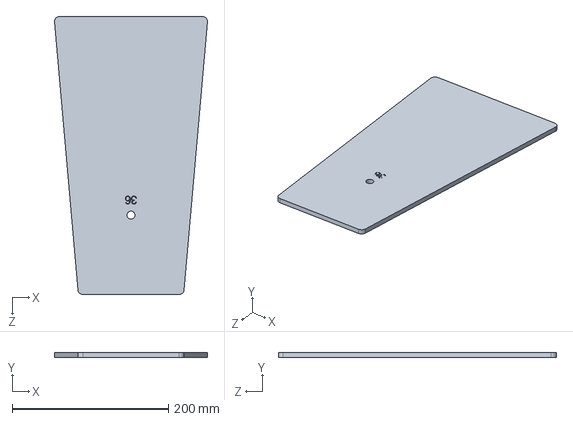
[picture p81: CAD file, 2026-05-23]
CAD/CNC Sled/Wedges/36 Segment Wedgie.SLDPRT
195.6 x 5.99 x 355.6 mm
