tonykoop/ashiko-drum-workshop/docs/Ashiko Makers Club/1inch keyed steel drive shaft.SLDPRT

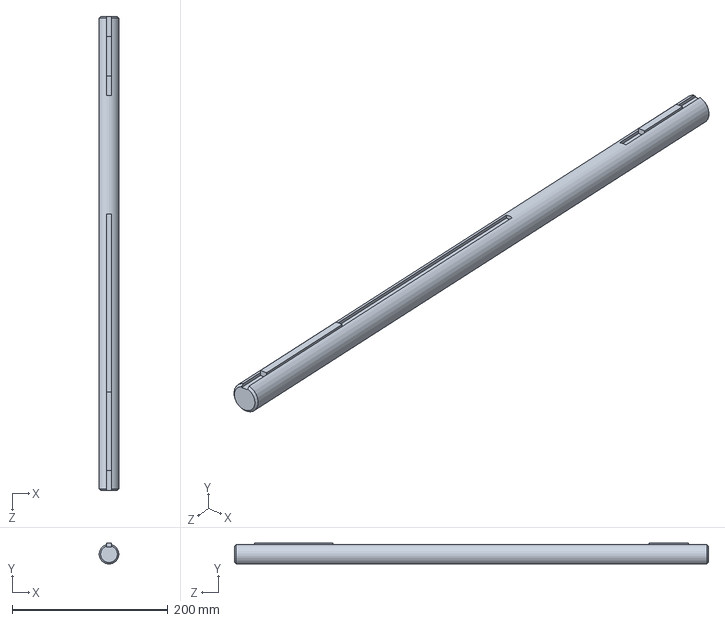
[picture p82: CAD file, 2026-04-25]
docs/Ashiko Makers Club/1inch keyed steel drive shaft.SLDPRT
25.3 x 26.9 x 609.6 mm
