tonykoop/ashiko-drum-workshop/CAD/CNC Sled/Sled Rear Side.SLDPRT

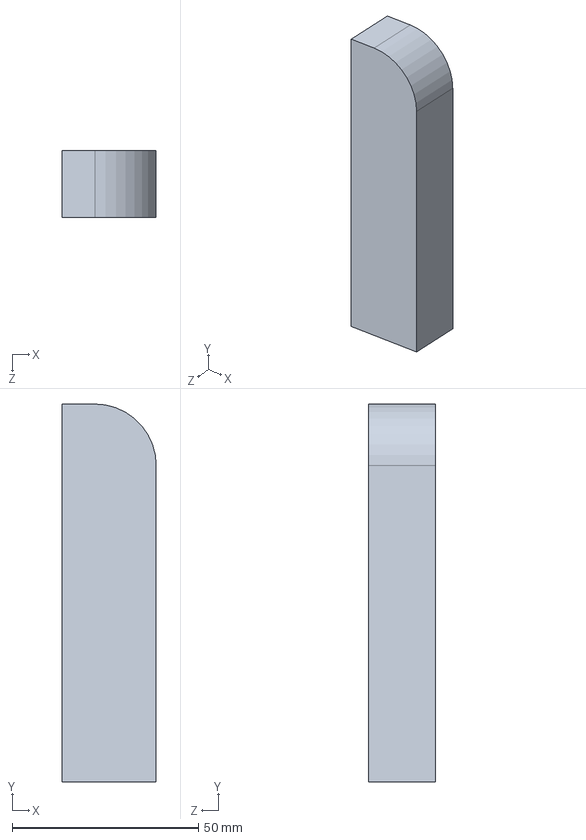
[picture p83: CAD file, 2026-05-23]
CAD/CNC Sled/Sled Rear Side.SLDPRT
25.4 x 101.6 x 18.0 mm
