tonykoop/ashiko-drum-workshop/CAD/CNC Sled/Wedges/20 Segment Wedge.SLDPRT

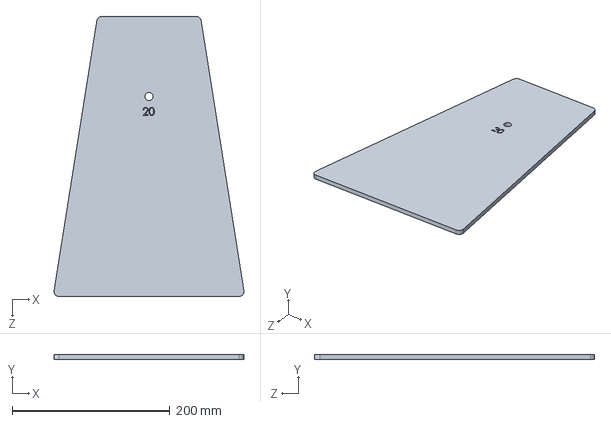
[picture p84: CAD file, 2026-05-23]
CAD/CNC Sled/Wedges/20 Segment Wedge.SLDPRT
241.2 x 5.99 x 355.6 mm
