tonykoop/ashiko-drum-workshop/docs/Ashiko Makers Club/Ashiko REV012316.SLDPRT

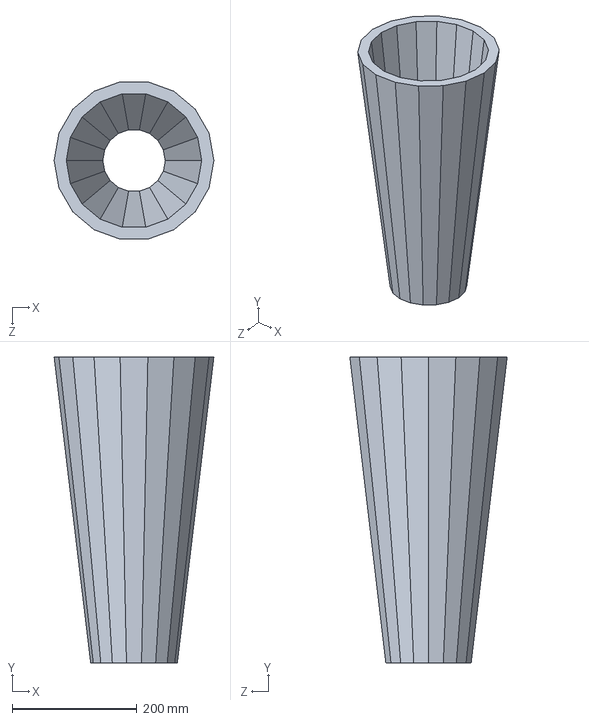
[picture p85: CAD file, 2026-04-25]
docs/Ashiko Makers Club/Ashiko REV012316.SLDPRT
256.0 x 490.2 x 252.1 mm
