tonykoop/ashiko-drum-workshop/CAD/CNC Sled/Sled Rear Top.SLDPRT

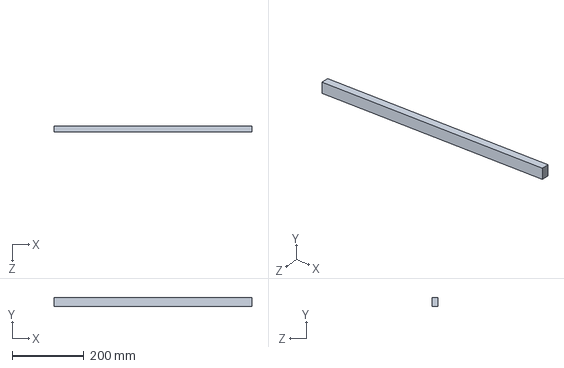
[picture p86: CAD file, 2026-05-23]
CAD/CNC Sled/Sled Rear Top.SLDPRT
552.5 x 25.4 x 18.0 mm
