tonykoop/ashiko-drum-workshop/CAD/CNC Sled/Wedges/16 Segment Wedgie.SLDPRT

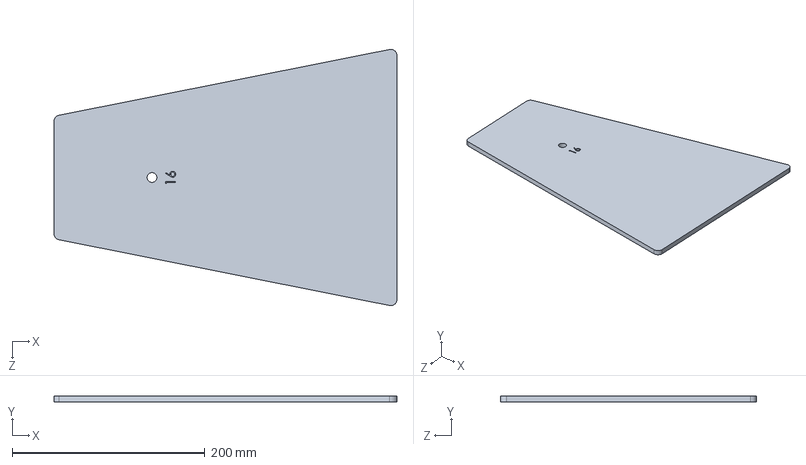
[picture p87: CAD file, 2026-05-23]
CAD/CNC Sled/Wedges/16 Segment Wedgie.SLDPRT
355.6 x 5.99 x 265.7 mm
