tonykoop/ashiko-drum-workshop/CAD/CNC Sled/CrossCut Arm A.SLDPRT

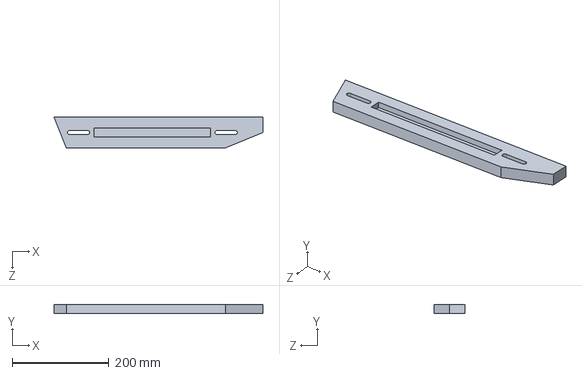
[picture p88: CAD file, 2026-05-23]
CAD/CNC Sled/CrossCut Arm A.SLDPRT
431.8 x 19.1 x 63.5 mm
