tonykoop/ashiko-drum-workshop/CAD/CNC Sled/Sliding Track - Short.SLDPRT

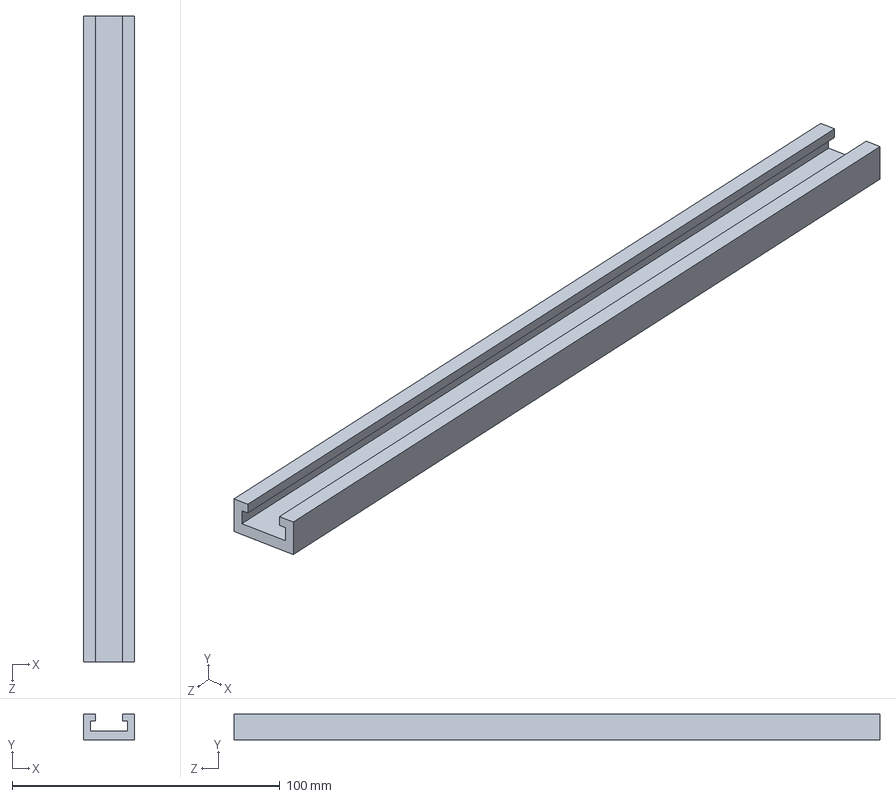
[picture p89: CAD file, 2026-05-23]
CAD/CNC Sled/Sliding Track - Short.SLDPRT
19.1 x 9.53 x 241.3 mm
