tonykoop/ashiko-drum-workshop/docs/Ashiko Makers Club/Ashiko REV010715.SLDPRT

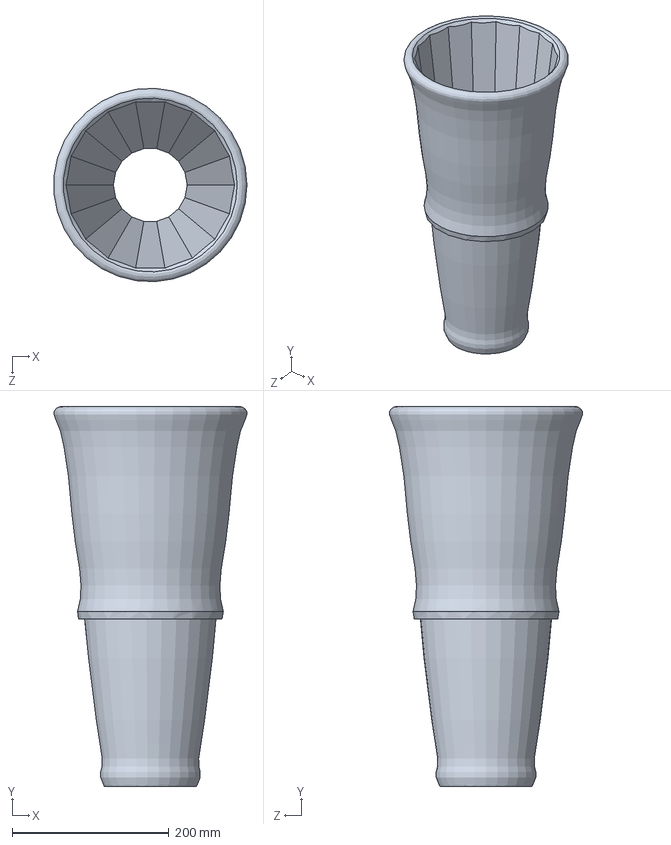
[picture p90: CAD file, 2026-04-25]
docs/Ashiko Makers Club/Ashiko REV010715.SLDPRT
246.3 x 485.1 x 246.6 mm
