tonykoop/ashiko-drum-workshop/CAD/CNC Sled/Stave Clamp Plate.SLDPRT

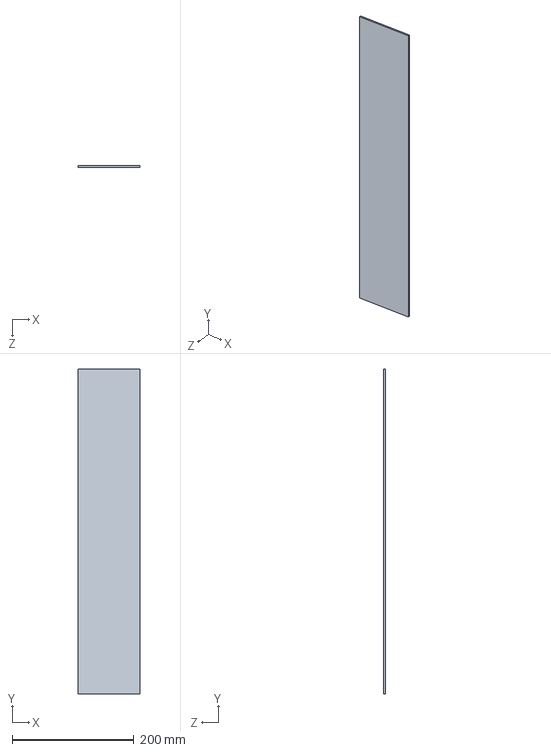
[picture p91: CAD file, 2026-05-23]
CAD/CNC Sled/Stave Clamp Plate.SLDPRT
101.6 x 533.4 x 3.00 mm
