tonykoop/ashiko-drum-workshop/CAD/CNC Sled/Sled Front.SLDPRT

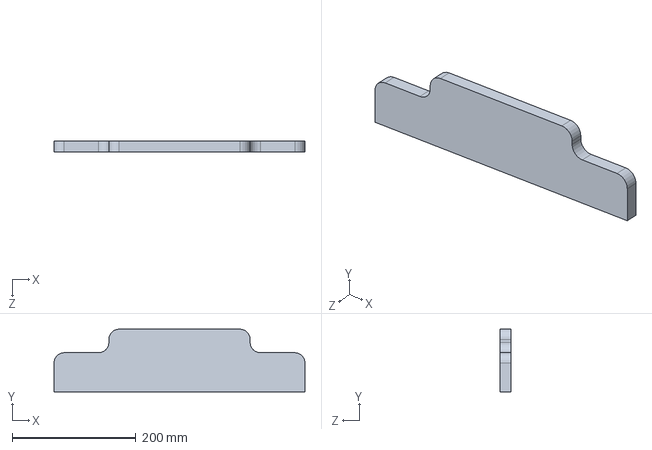
[picture p92: CAD file, 2026-05-23]
CAD/CNC Sled/Sled Front.SLDPRT
406.4 x 101.6 x 18.0 mm
