tonykoop/ashiko-drum-workshop/docs/Ashiko Makers Club/Five Eighths Arbor to 60 Degree Cone Adapter.SLDPRT

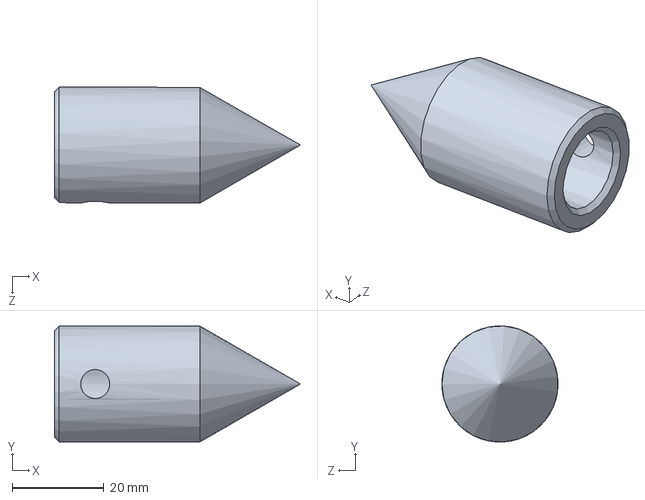
[picture p93: CAD file, 2026-04-25]
docs/Ashiko Makers Club/Five Eighths Arbor to 60 Degree Cone Adapter.SLDPRT
53.7 x 25.3 x 25.4 mm
