tonykoop/ashiko-drum-workshop/docs/Ashiko Makers Club/1inch Collar Flange.SLDPRT

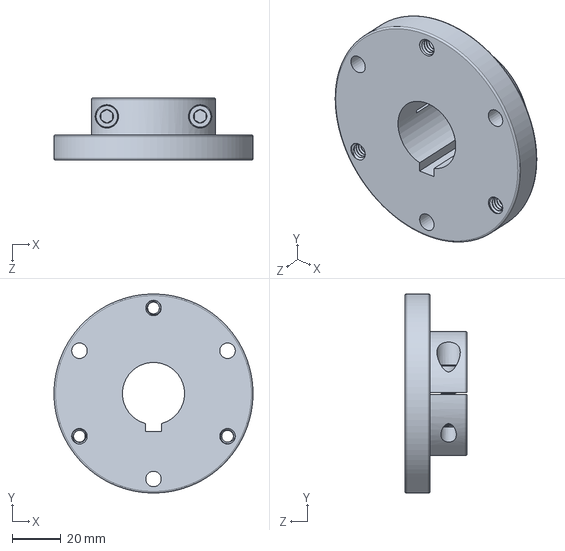
[picture p94: CAD file, 2026-04-25]
docs/Ashiko Makers Club/1inch Collar Flange.SLDPRT
81.3 x 81.2 x 25.4 mm
