tonykoop/ashiko-drum-workshop/docs/Ashiko Makers Club/Ashiko REV010915.SLDPRT

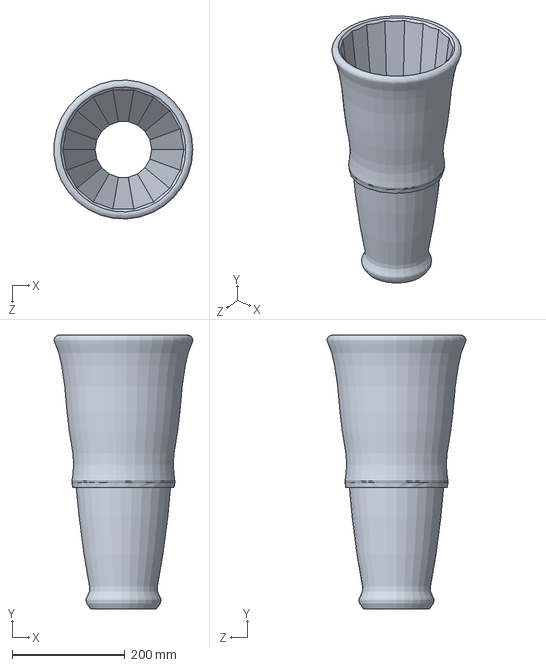
[picture p95: CAD file, 2026-04-25]
docs/Ashiko Makers Club/Ashiko REV010915.SLDPRT
246.5 x 486.9 x 246.7 mm
