tonykoop/ashiko-drum-workshop/docs/Ashiko Makers Club/Ashiko REV010815.SLDPRT

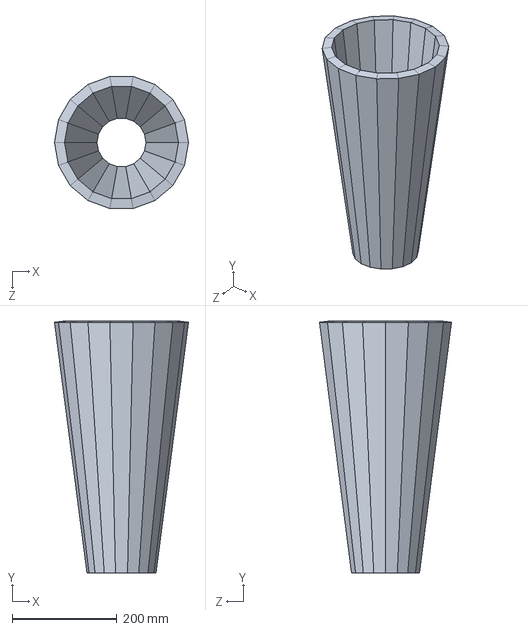
[picture p96: CAD file, 2026-04-25]
docs/Ashiko Makers Club/Ashiko REV010815.SLDPRT
256.0 x 481.1 x 252.1 mm
