tonykoop/ashiko-drum-workshop/docs/Ashiko Makers Club/1inch keyed steel drive shaft V2.SLDPRT

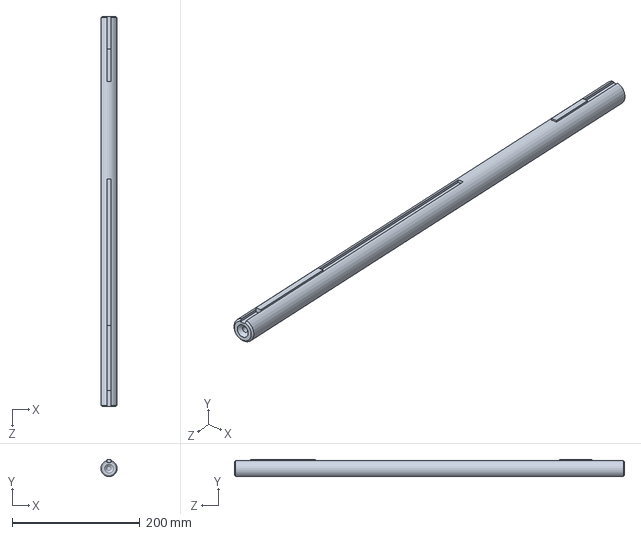
[picture p97: CAD file, 2026-04-25]
docs/Ashiko Makers Club/1inch keyed steel drive shaft V2.SLDPRT
25.3 x 26.9 x 609.6 mm
