tonykoop/ashiko-drum-workshop/docs/Ashiko Makers Club/PDFs/Stave Draft Rounds 1-7.pdf

Ashiko Maker | Round 1 | Round 2 | Round 3 | Round 4 | Round 5 | Round 6 | Round 7
1 | Mike Nieland
2 | Max Okray
3 | Joe Spitzenberger
4 | Dallas Nustvold
5 | Dan Estenson
6 | Tyler Kilbury
7 | Tony Koop
8 | Spare Drum #1
9 | Spare Drum #2
10 | Spare Drum #3
11 | Spare Drum #4
12 | Spare Drum #5
13 | Spare Drum Extra
