tonykoop/ashiko-drum-workshop/docs/Ashiko Makers Club/Ashiko Drums/392.jpg

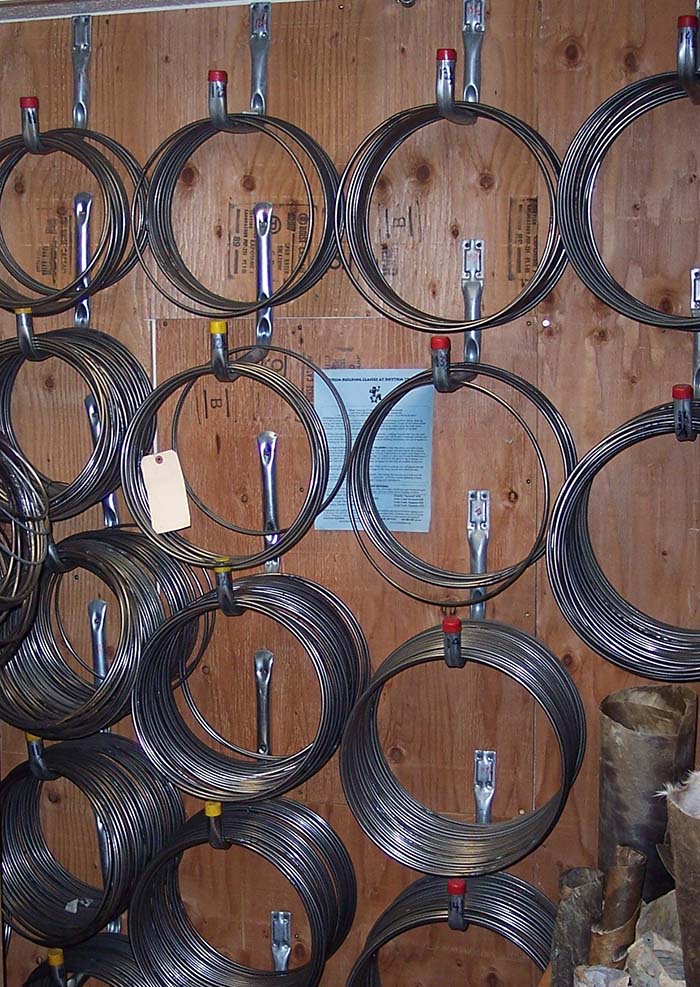
docs/Ashiko Makers Club/Ashiko Drums/392.jpg
