tonykoop/ashiko-drum-workshop/docs/Ashiko Makers Club/Ashiko Drums/3177614_orig.jpg

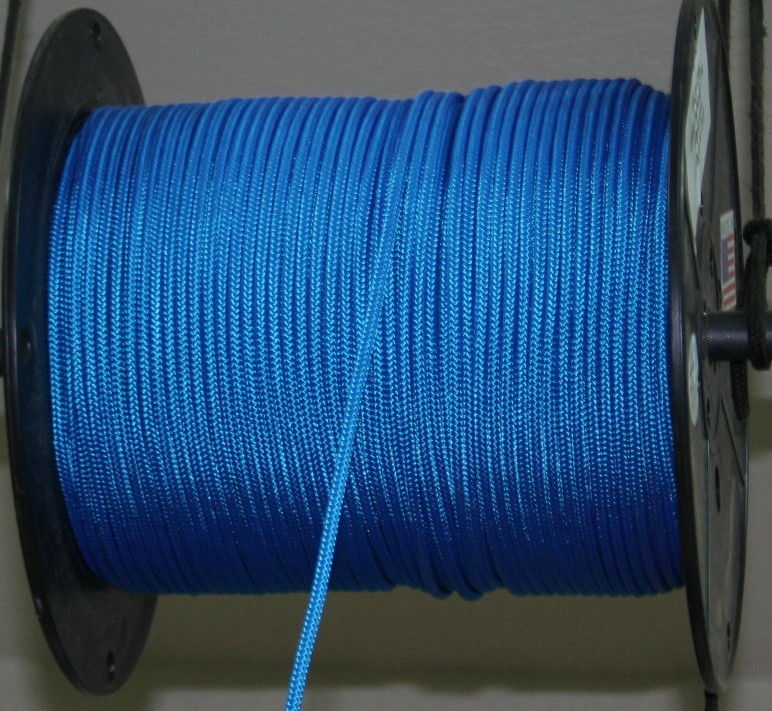
docs/Ashiko Makers Club/Ashiko Drums/3177614_orig.jpg
