tonykoop/ashiko-drum-workshop/docs/Ashiko Makers Club/Ashiko Drums/4814250.jpg

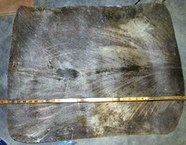
docs/Ashiko Makers Club/Ashiko Drums/4814250.jpg
