tonykoop/ashiko-drum-workshop/docs/Ashiko Makers Club/Ashiko Drums/all prints small.jpg

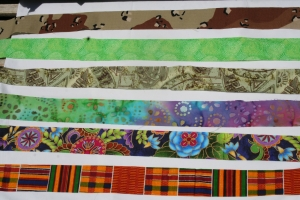
docs/Ashiko Makers Club/Ashiko Drums/all prints small.jpg
