tonykoop/ashiko-drum-workshop/docs/Ashiko Makers Club/Ashiko Drums/Ashiko Stave 3 View of Top.JPG

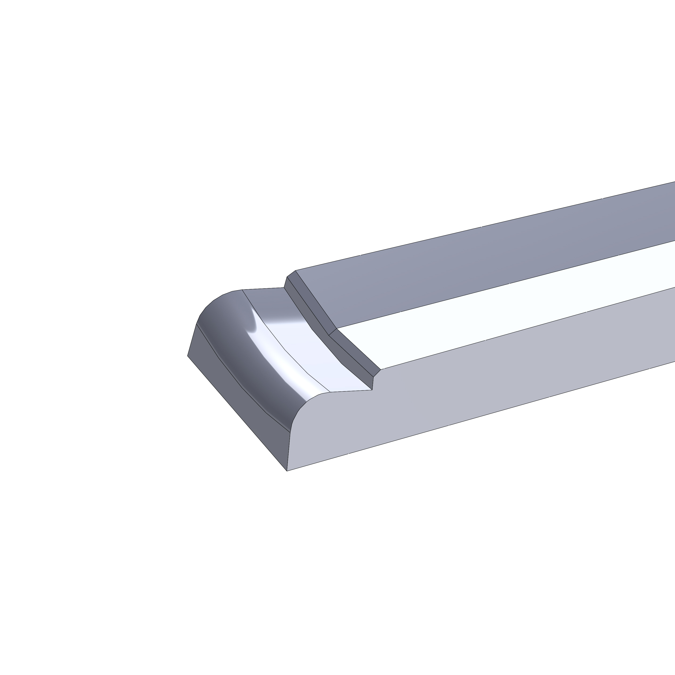
docs/Ashiko Makers Club/Ashiko Drums/Ashiko Stave 3 View of Top.JPG
