tonykoop/ashiko-drum-workshop/docs/Ashiko Makers Club/Ashiko Drums/Ashiko.jpg

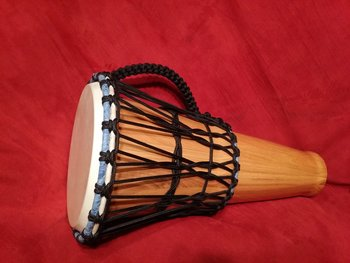
docs/Ashiko Makers Club/Ashiko Drums/Ashiko.jpg
