tonykoop/ashiko-drum-workshop/docs/Ashiko Makers Club/Ashiko Drums/rsz_392.jpg

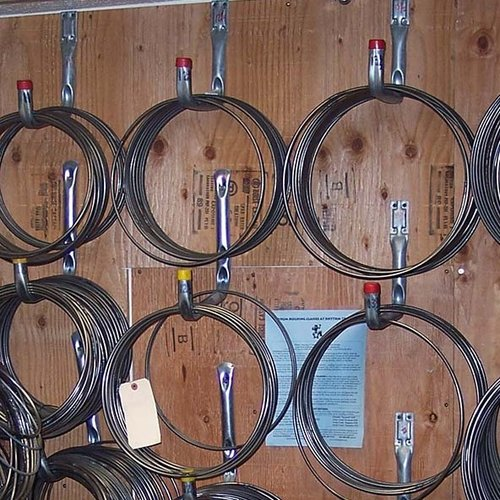
docs/Ashiko Makers Club/Ashiko Drums/rsz_392.jpg
