tonykoop/ashiko-drum-workshop/docs/Ashiko Makers Club/Ashiko Drums/rsz_2014-11-19_173639.jpg

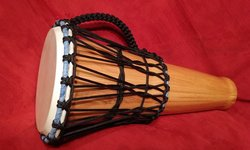
docs/Ashiko Makers Club/Ashiko Drums/rsz_2014-11-19_173639.jpg
