tonykoop/ashiko-drum-workshop/docs/Ashiko Makers Club/Spokes/15 Spoke.PDF

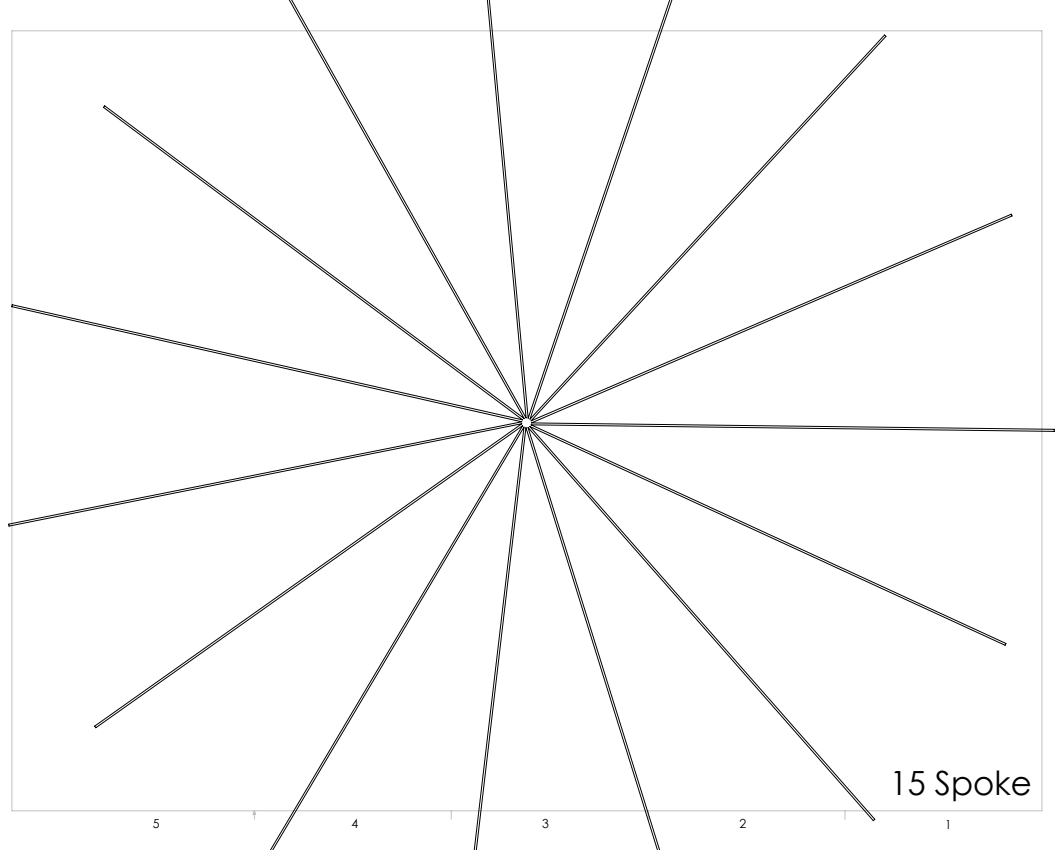
[picture p128: page 1]
15 Spoke
