tonykoop/ashiko-drum-workshop/docs/Ashiko Makers Club/Spokes/16 Spoke.PDF

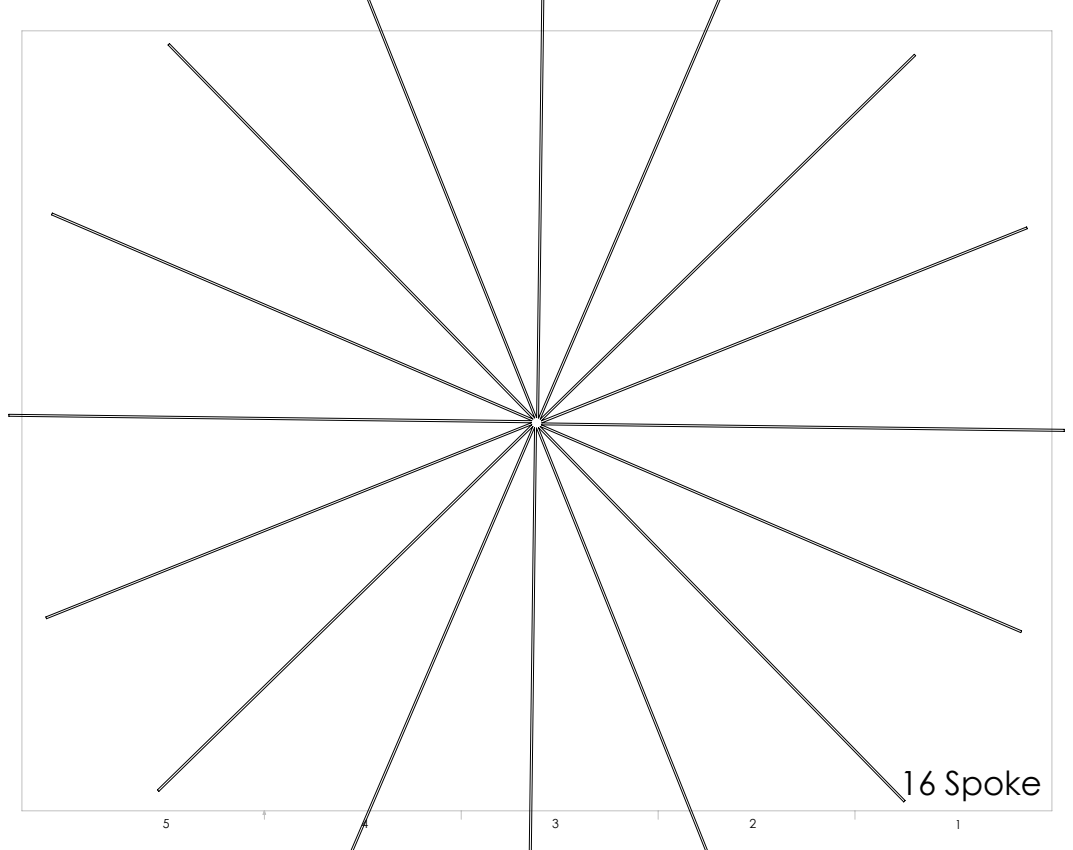
[picture p129: page 1]
16 Spoke
