tonykoop/ashiko-drum-workshop/docs/Ashiko Makers Club/Spokes/17 Spoke.PDF

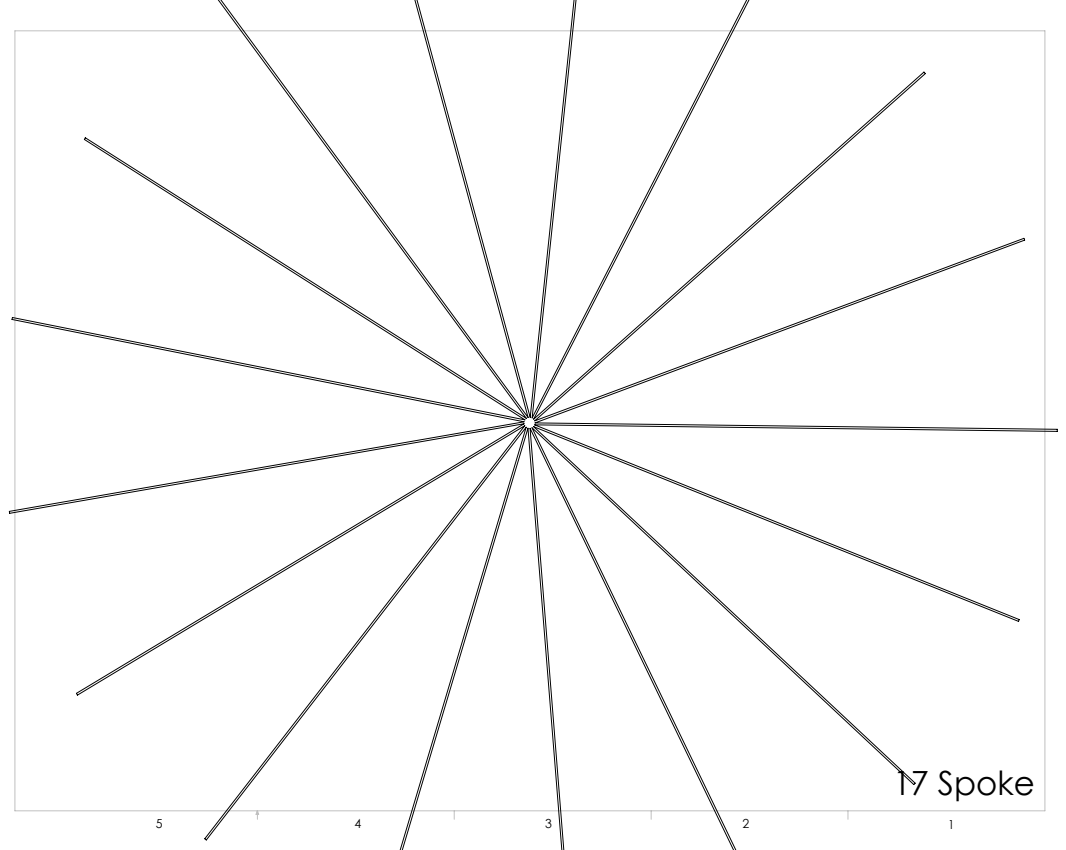
[picture p130: page 1]
17 Spoke
