tonykoop/ashiko-drum-workshop/docs/Ashiko Makers Club/Spokes/18 Spoke.PDF

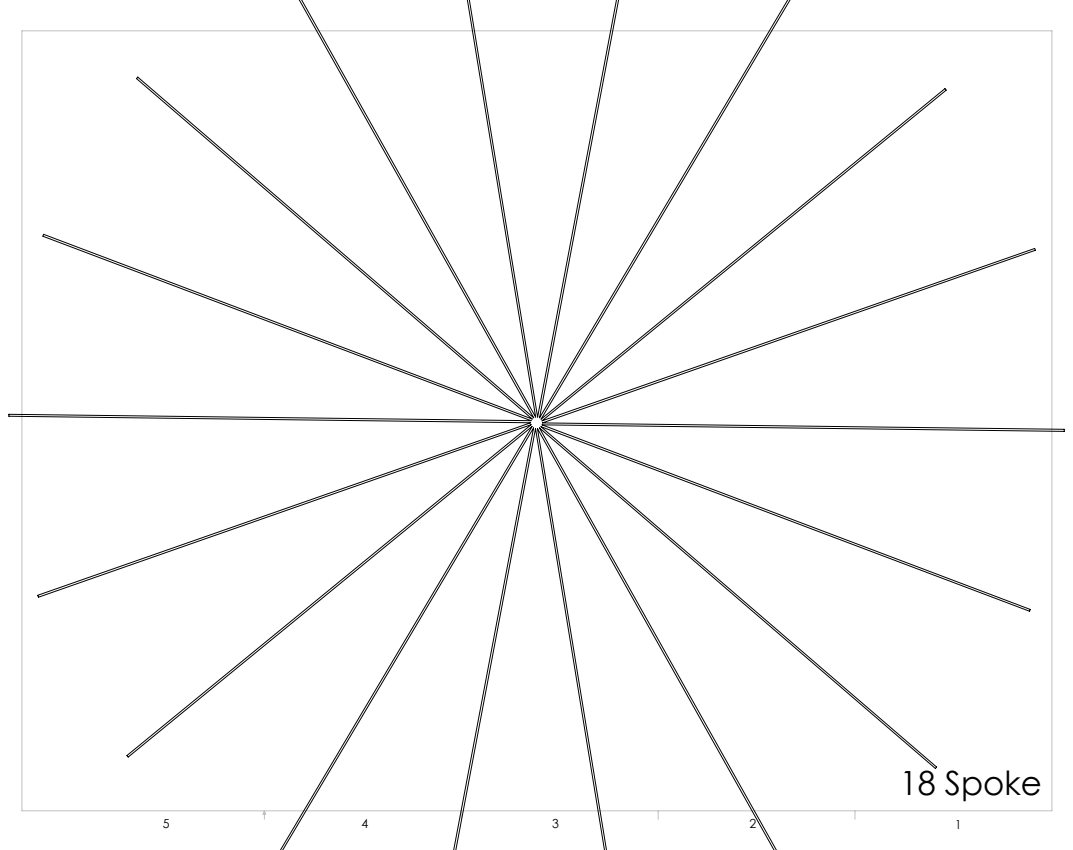
[picture p131: page 1]
18 Spoke
