tonykoop/ashiko-drum-workshop/images/20210320_130448.jpg

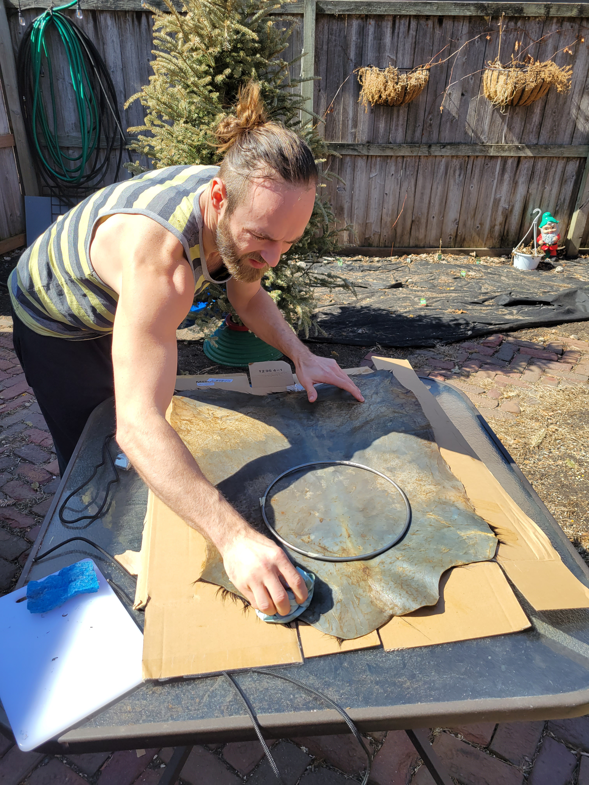
images/20210320_130448.jpg
